tobiasdruckt/SGNode/.openhands/librarian/files/SGNode_Plug_SGNode_Plug.md

# SGNode_Plug/SGNode_Plug.ino

**Type:** Arduino Sketch
**Hash:** `328629a377f053a2d4831d89c57e913e6fd26ec8657b2f4a0ddb5f2aaffe9b44`

## Role

Plug temperature controller entry point with PI control and ESP-NOW communication.

## Verified API / Symbols

## Key Dependencies

- plug_hardware.h, src/air_controller.h, src/beer_pi_controller.h, src/plug_sensors.h, src/plug_selfcheck.h

## Side Effects

- Temperature target calculation

## Tests

- No dedicated automated test identified

## Change Risks

- **MEDIUM**: Core functionality change

---
*Last modified (hash): 328629a377f053a2d4831d89c57e913e6fd26ec8657b2f4a0ddb5f2aaffe9b44*
