tobiasdruckt/SGNode/.openhands/librarian/files/SGNode_Plug_src_air_controller.md

# SGNode_Plug/src/air_controller.h

**Type:** C++ Header
**Hash:** `8307e315ba311d8ae50e1e14f3aa872aa893262df997e26e768ca7ebc397dfbf`

## Role

Fridge air temperature target calculation from beer target.

## Verified API / Symbols

- Structs: AirControllerConfig
- Classes: AirController

- Functions: update, setConfig, relayOn, lastChangeMs

## Key Dependencies

- beer_pi_controller.h

## Side Effects

- No significant side effects

## Tests

- No dedicated automated test identified

## Change Risks

- **MEDIUM**: Core functionality change

---
*Last modified (hash): 8307e315ba311d8ae50e1e14f3aa872aa893262df997e26e768ca7ebc397dfbf*
