tobiasdruckt/SGNode/.openhands/librarian/files/SGNode_Plug_src_plug_types.md

# SGNode_Plug/src/plug_types.h

**Type:** C++ Header
**Hash:** `ce8625bc8ce176ee42a78beea442ccf4ed55586093ea766cdf19b6ec3cb79450`

## Role

Header file with declarations.

## Verified API / Symbols

- Structs: SensorSnapshot
- Classes: PlugControlMode
- Enums: class, PlugFault

## Key Dependencies

- Arduino.h, sg_protocol.h

## Side Effects

- No significant side effects

## Tests

- No dedicated automated test identified

## Change Risks

- **MEDIUM**: Core functionality change

---
*Last modified (hash): ce8625bc8ce176ee42a78beea442ccf4ed55586093ea766cdf19b6ec3cb79450*
