tobiasdruckt/SGNode/.openhands/librarian/files/SGNode_Plug_src_plug_selfcheck_h.md

# SGNode_Plug/src/plug_selfcheck.h

**Type:** C++ Header
**Hash:** `57b49919bb82ef1c21641c5f9edea90fe9c7763b2bc4e47531cef4ad020f714f`

## Overview / Role

Core functionality module

## Verified API & Symbols

No API symbols found or file type not supported

## Key Dependencies

**System/External:**
- `<Arduino.h>`

## Side Effects & Hardware Access

- No significant side effects

## Change Risks

- **MEDIUM**: Core functionality change

---
*Last modified (hash): 57b49919bb82ef1c21641c5f9edea90fe9c7763b2bc4e47531cef4ad020f714f*
