tobiasdruckt/SGNode/.openhands/librarian/files/SGNode_Base_src_calculations_brix_converter.md

# SGNode_Base/src/calculations/brix_converter.h

**Type:** C++ Header
**Hash:** `5e41e067330df2d826816df89a01c500e7435dedcccd328aad6d9078b4e3edc9`

## Role

Brix to SG conversion using calibration polynomial.

## Verified API / Symbols

- Classes: BrixConverter

- Functions: brixToSG

## Key Dependencies

- polynomial_calibration.h

## Side Effects

- No significant side effects

## Tests

- No dedicated automated test identified

## Change Risks

- **MEDIUM**: Calculation changes affect data accuracy

---
*Last modified (hash): 5e41e067330df2d826816df89a01c500e7435dedcccd328aad6d9078b4e3edc9*
