tobiasdruckt/SGNode/.openhands/librarian/files/SGNode_Base_src_calculations_target_curve.md

# SGNode_Base/src/calculations/target_curve.h

**Type:** C++ Header
**Hash:** `1c5d0c6030944191cfbcedbfc1d03d2b40349b1e07c24ff98de612adee10b815`

## Role

Temperature target curve generation.

## Verified API / Symbols

- Classes: TargetCurveGenerator

- Functions: generateAndSave, expectedGravityAtHour, expectedAttenuationAtHour

## Key Dependencies

- brew_profile.h

## Side Effects

- No significant side effects

## Tests

- No dedicated automated test identified

## Change Risks

- **MEDIUM**: Calculation changes affect data accuracy

---
*Last modified (hash): 1c5d0c6030944191cfbcedbfc1d03d2b40349b1e07c24ff98de612adee10b815*
