tobiasdruckt/SGNode/.openhands/librarian/files/SGNode_Base_src_domain_batch_action.md

# SGNode_Base/src/domain/batch_action.h

**Type:** C++ Header
**Hash:** `cc4561e8239351c93ec19e92246e3ac046810b8edf2029d3946a3bc6921fdaf9`

## Role

Batch data structures and state management.

## Verified API / Symbols

- Structs: BatchAction
- Classes: BatchActionEngine
- Enums: BatchActionType

- Functions: applyStyleDefaults, applyDone, applySkip

## Key Dependencies

- Arduino.h
- FS.h, SD.h (for batch persistence)

## Side Effects

- No significant side effects

## Tests

- No dedicated automated test identified

## Change Risks

- **MEDIUM**: Domain logic affects business rules

---
*Last modified (hash): cc4561e8239351c93ec19e92246e3ac046810b8edf2029d3946a3bc6921fdaf9*
