tobiasdruckt/SGNode/.openhands/librarian/files/SGNode_Base_src_domain_fermentation_state_machine.md

# SGNode_Base/src/domain/fermentation_state_machine.h

**Type:** C++ Header
**Hash:** `c94df5f87726f569a1de4751b6daa8bea19875daa21fbb661194700243f60946`

## Role

Fermentation state machine and phase tracking.

## Verified API / Symbols

- Classes: FermentationStateMachine
- Enums: FermentationPhase

- Functions: reset

## Key Dependencies

- Arduino.h
- batch_action.h

## Side Effects

- No significant side effects

## Tests

- No dedicated automated test identified

## Change Risks

- **HIGH**: State machine affects batch tracking

---
*Last modified (hash): c94df5f87726f569a1de4751b6daa8bea19875daa21fbb661194700243f60946*
