tobiasdruckt/SGNode/.openhands/librarian/files/SGNode_Base_src_domain_yeast_preset.md

# SGNode_Base/src/domain/yeast_preset.h

**Type:** C++ Header
**Hash:** `b73fa077c95b8817bcb092ea003f989cab3516cdc6004e01fa5ec9d90076fd9a`

## Role

Yeast preset configuration and repository.

## Verified API / Symbols

- Structs: YeastPreset

## Key Dependencies

- Arduino.h
- FS.h, SD.h (for yeast file storage)

## Side Effects

- No significant side effects

## Tests

- No dedicated automated test identified

## Change Risks

- **MEDIUM**: Domain logic affects business rules

---
*Last modified (hash): b73fa077c95b8817bcb092ea003f989cab3516cdc6004e01fa5ec9d90076fd9a*
