tobiasdruckt/SGNode/.openhands/librarian/files/SGNode_Base_src_domain_yeast_preset_repository.md

# SGNode_Base/src/domain/yeast_preset_repository.h

**Type:** C++ Header
**Hash:** `1a147f964cd8618a893252e45a2800361be83310e576e99de19c2c4fcf8ad808`

## Role

Yeast preset configuration and repository.

## Verified API / Symbols

- Classes: YeastPresetRepository

- Functions: invalidateCache, reloadCustom, count, applyToProfile, isCustom, saveCustom, deleteCustom

## Key Dependencies

- Arduino.h
- FS.h, SD.h (for yeast file storage)

## Side Effects

- No significant side effects

## Tests

- No dedicated automated test identified

## Change Risks

- **MEDIUM**: Domain logic affects business rules

---
*Last modified (hash): 1a147f964cd8618a893252e45a2800361be83310e576e99de19c2c4fcf8ad808*
