tobiasdruckt/SGNode/.openhands/librarian/files/SGNode_Base_src_ui_brew_wizard_controller.md

# SGNode_Base/src/ui/brew_wizard_controller.h

**Type:** C++ Header
**Hash:** `402d01940dfb781f971f2dc086219334e5958b499bc3ebb8d340eff37e6c521d`

## Role

Touchscreen UI components for base station.

## Verified API / Symbols

- Classes: WizardStepper, VirtualKeyboardInput, StyleDropdown, AttenuationDropdown, IOSSwitch
- Enums: BrewWizardStep

- Functions: draw, handleTextTouch, handleNumberTouch, drawText, drawNumber, count, valueAt, hit, begin, handleTouch

## Key Dependencies

- Arduino.h
- TFT_eSPI.h

## Side Effects

- Touchscreen UI updates

## Tests

- No dedicated automated test identified

## Change Risks

- **MEDIUM**: UI changes affect user experience

---
*Last modified (hash): 402d01940dfb781f971f2dc086219334e5958b499bc3ebb8d340eff37e6c521d*
