tobiasdruckt/SGNode/.openhands/librarian/files/SGNode_Base_src_ui_ui_tokens.md

# SGNode_Base/src/ui/ui_tokens.h

**Type:** C++ Header
**Hash:** `b66e78fc84c8e0ac1aaf987366e8da169580bf831fdd6b88a70602f1c9a8864e`

## Role

Touchscreen UI components for base station.

## Verified API / Symbols

- Functions: rgb565, uiInitColors

## Key Dependencies

- Arduino.h
- TFT_eSPI.h

## Side Effects

- No significant side effects

## Tests

- No dedicated automated test identified

## Change Risks

- **MEDIUM**: UI changes affect user experience

---
*Last modified (hash): b66e78fc84c8e0ac1aaf987366e8da169580bf831fdd6b88a70602f1c9a8864e*
