tobiasdruckt/SGNode/.openhands/librarian/files/SGNode_Plug_src_plug_selfcheck.md

# SGNode_Plug/src/plug_selfcheck.h

**Type:** C++ Header
**Hash:** `57b49919bb82ef1c21641c5f9edea90fe9c7763b2bc4e47531cef4ad020f714f`

## Role

Header file with declarations.

## Verified API / Symbols

- Functions: runPlugSelfChecks

## Key Dependencies

- Arduino.h

## Side Effects

- No significant side effects

## Tests

- No dedicated automated test identified

## Change Risks

- **MEDIUM**: Core functionality change

---
*Last modified (hash): 57b49919bb82ef1c21641c5f9edea90fe9c7763b2bc4e47531cef4ad020f714f*
