tobiasdruckt/SGNode/.openhands/librarian/files/SGNode_Plug_src_plug_transport.md

# SGNode_Plug/src/plug_transport.h

**Type:** C++ Header
**Hash:** `c5f03b4bd983e4b1c55153e3edbc8ea55bb9e342c8efd9fb4064104756ac84df`

## Role

ESP-NOW transport layer for Plug communication.

## Verified API / Symbols

- Classes: PlugTransport

- Functions: begin, hasCommand, lastCommandMs, sendStatus, onReceive

## Key Dependencies

- Arduino.h
- sg_protocol.h
- esp_now.h

## Side Effects

- No significant side effects

## Tests

- No dedicated automated test identified

## Change Risks

- **MEDIUM**: Core functionality change

---
*Last modified (hash): c5f03b4bd983e4b1c55153e3edbc8ea55bb9e342c8efd9fb4064104756ac84df*
