tobiasdruckt/SGNode/RELEASE_NOTES_v0.3.0-alpha.md

# SGNode v0.3.0-alpha Release Notes

> Historical archive. Current documentation and active release notes are in `README.md` and `RELEASE_NOTES_v0.5.0-alpha.md`.

**Release Date:** May 6, 2026  
**Status:** Design Freeze - Alpha Release  

## Overview

SGNode v0.3.0-alpha marks a significant milestone with complete system stabilization, comprehensive calibration functionality, and robust data management. This release introduces critical fixes for polynomial calibration, SD card file corruption, and battery voltage accuracy, establishing a solid foundation for fermentation monitoring.

## 🎯 Design Freeze Features

### Confirmed Working Systems
- ✅ **Peer-to-Peer Communication** - Reliable ESP-NOW data transmission with retry logic
- ✅ **Calibration System** - Complete 4-point calibration with 3rd degree polynomial calculation
- ✅ **Data Logging** - Robust CSV file creation and SD card storage with corruption prevention
- ✅ **Real-time Display** - Live, Graph, and Detail views with immediate data display after reboot
- ✅ **Battery Monitoring** - Accurate voltage measurement with calibrated voltage divider
- ✅ **Historical Data Persistence** - Automatic data loading and file continuation across reboots

### System Safeguards
- 🛡️ **Communication Reliability** - CRC16 verification, peer management, channel forcing
- 🛡️ **Sensor Protection** - Initialization retry, watchdog timer, voltage sanity checks
- 🛡️ **Calibration Safety** - Matrix singularity detection, coefficient validation, EEPROM versioning
- 🛡️ **File System Protection** - Write verification, extension validation, automatic recovery
- 🛡️ **Power Management** - GPIO optimization, deep sleep protection, battery monitoring

## 🔧 Critical Fixes

### Polynomial Calibration System
- **Fixed matrix back substitution** - Corrected RHS extraction from augmented matrix
- **Fixed coefficient mapping** - Simplified nested ternary operators to clear if/else structure
- **Added debug output** - Coefficient logging for verification and troubleshooting
- **Result**: Calibration now produces accurate polynomial coefficients instead of all zeros

### Base Station Communication
- **Fixed rate limiting** - Reset rate limiting before final calibration response transmission
- **Enhanced error handling** - Better ESP-NOW error reporting and recovery
- **Result**: Base station receives completion message and shows "Calibration Success"

### SD Card File System
- **Fixed file corruption** - Added filename validation preventing .c file creation
- **Enhanced file management** - Sequential numbering (fermentation_001.csv, etc.)
- **Added historical loading** - Automatic CSV data loading on reboot (up to 100 points)
- **Result**: No more corrupted files, seamless data continuation across reboots

### Battery Voltage Accuracy
- **Updated calibration factor** - Changed from 0.913 to 1.048 (13% error correction)
- **Added voltage divider spec** - 51kΩ:51kΩ with 10µF filtering capacitor
- **Enhanced SOC calculation** - More accurate battery percentage display
- **Result**: 4.062V battery now reads correctly as ~4.06V

## 📊 Technical Improvements

### Data Management
- **CSV format standardization** - Consistent column ordering and metadata
- **OG capture persistence** - Original Gravity restored from CSV comments on reboot
- **File integrity verification** - Byte count validation for all SD writes
- **Automatic file recovery** - Creates new file if corruption detected

### Power Optimization
- **Deep sleep enhancement** - Proper WiFi/ESP-NOW deinitialization
- **GPIO leakage prevention** - All unused pins configured as OUTPUT LOW
- **Battery monitoring** - Real-time SOC with low-battery warnings
- **Charging protection** - Built-in over-charge/discharge protection

### User Experience
- **Calibration wizard reliability** - Consistent command transmission and response
- **Immediate data display** - Views show historical data immediately after reboot
- **Touch interface responsiveness** - Improved navigation and status indicators
- **Debug system** - Comprehensive conditional compilation levels

## 🔧 Hardware Specifications

### Float Unit
- **WeMos D32 ESP32** with built-in 18650 battery holder
- **BMI160 IMU** - 6-axis accelerometer/gyroscope
- **BMP180** - Temperature/pressure sensor
- **Voltage Divider** - 51kΩ:51kΩ with 10µF capacitor
- **Calibration Switch** - GPIO12 hardware switch activation

### Base Station
- **4.0inch ESP32-32E** - Integrated display with touch screen
- **SD Card Support** - FAT32 formatted, 4GB+ recommended
- **Power Supply** - 5V USB, ~290mA consumption

## 📈 Performance Metrics

### Accuracy
- **Tilt measurement**: ≤0.5° angle resolution
- **SG accuracy**: ±0.001 with proper calibration
- **Temperature**: ±0.1°C with EMA filtering
- **Battery voltage**: ±1% after calibration

### Battery Life
- **Float continuous**: 17+ hours
- **Float deep sleep**: 2-4 weeks (2000mAh 18650)
- **Base station**: Continuous operation on USB power

### Communication
- **Range**: ~50m line of sight
- **Update rate**: 60-600 seconds (default 180s)
- **Reliability**: CRC16 verification, 3-retry logic

## 🚀 Future Roadmap (Post-Alpha)

### Planned Improvements
- **UI and Theme Enhancements** - Improved visual design and user interface
- **Clock Integration** - Real-time clock in base station
- **3D Printed Housing** - Waterproof float enclosure design
- **Liquid Behavior Testing** - Real-world fermentation testing
- **Enhanced Data Visualization** - Improved graphs and analytics
- **Wireless Configuration** - OTA updates and remote configuration

### Development Focus
- **User Experience** - Streamlined setup and operation
- **Data Analysis** - Advanced fermentation analytics
- **Connectivity** - Enhanced wireless features
- **Power Efficiency** - Further battery optimization

## 📋 Installation Requirements

This library and hardware list describes the archived v0.3.0 build only. Current requirements are documented in `README.md`.

### Required Libraries
- **Float Unit**: EmotiBit BMI160, Adafruit BMP085
- **Base Station**: TFT_eSPI, SD (built-in), FS (built-in)

### Hardware Components
- **Float Unit**: WeMos D32, BMI160, BMP180, 18650 battery, SPST switch
- **Base Station**: 4.0inch ESP32-32E display, MicroSD card, USB power

### Setup Steps
1. Install required libraries via Arduino IDE
2. Configure base station MAC address in float unit
3. Upload firmware to both devices
4. Perform 4-point calibration
5. Start fermentation monitoring

## 🎯 Design Freeze Status

This v0.3.0-alpha release establishes a **design freeze** for the core functionality. All confirmed features are working reliably, and the system is ready for real-world testing.

### What's Frozen
- ✅ Core communication protocol (ESP-NOW)
- ✅ Calibration system and algorithms
- ✅ Data logging and file management
- ✅ User interface and navigation
- ✅ Battery monitoring and power management
- ✅ Safety systems and error handling

### What's Open for Development
- 🔧 UI themes and visual improvements
- 🔧 Clock integration and time features
- 🔧 3D printed housing design
- 🔧 Advanced analytics and data visualization
- 🔧 Wireless configuration and OTA updates

## 📝 Support and Documentation

- **README.md** - Comprehensive setup and operation guide
- **WIRING_DIAGRAM.md** - Detailed hardware connections
- **hardware.md** - Bill of materials and specifications
- **CHANGELOG.md** - Complete version history
- **Serial Monitor** - Debug output and troubleshooting

---

**This release represents a stable foundation for fermentation monitoring with all core features confirmed working. The system is ready for practical use and further development of advanced features.**
