tobiasdruckt/SGNode/SGNode_Base/SGNode_Base.ino

/*
 * Fermentation Monitor - Base Station
 * Receives data via ESP-NOW and displays on TFT with touch interface
 * Shows real-time data and historical graphs
 * 
 * REQUIRED LIBRARIES (install via Arduino Library Manager):
 * - TFT_eSPI (by Bodmer) - includes built-in touch support
 * - SD (built-in)
 * - FS (built-in)
 * - SPI (built-in)
 */

#include <WiFi.h>
#include <esp_now.h>
#include <WebServer.h>
#include <Update.h>
#include <TFT_eSPI.h>
#include <FS.h>
#include <SD.h>
#include <SPI.h>
#include <Wire.h>
#include <EEPROM.h>
#include <time.h>
#include <sys/time.h>
#include "src/assets/Logo2_Optimized.h"
#include "src/ui/ui_tokens.h"
#include "src/ui/ui_components.h"
#include "src/domain/brew_profile.h"
#include "src/ui/brew_wizard_controller.h"
#include "src/calculations/brix_converter.h"
#include "src/calculations/og_verifier.h"
#include "src/calculations/derived_calculations.h"
#include "src/calculations/target_curve.h"
#include "src/domain/fermentation_state_machine.h"
#include "src/domain/recommendation_engine.h"
#include "src/calculations/eta_predictor.h"
#include "src/domain/batch_action.h"
#include "src/domain/yeast_preset_repository.h"
#include "src/domain/temperature_profile.h"
#ifndef SGNODE_UI_TEST_HARNESS
#define SGNODE_UI_TEST_HARNESS 0  // Debug-only serial UI harness. Keep disabled for production builds.
#endif
#ifndef SGNODE_UI_TEST_MINIMAL
#define SGNODE_UI_TEST_MINIMAL 0  // 1 = minimal harness commands (no UI injection path)
#endif

#ifndef SGNODE_BATTERY_DEBUG
#define SGNODE_BATTERY_DEBUG 0  // Tiny serial diagnostics for battery/history checks. Disabled in production.
#endif
#include "src/test/ui_test_harness.h"
#include "../SGNode_Shared/sg_protocol.h"
#include "../SGNode_Shared/sg_logo_png.h"
#include "src/calculations/polynomial_calibration.h"

#define ACK_PACKET_TYPE 0xA5

// 4.0inch ESP32-32E Display configuration - ST7796S landscape mode
#define SCREEN_W    480  // Landscape width (320x480 native rotated)
#define SCREEN_H    320  // Landscape height
#define DISPLAY_CS  15   // LCD Chip Select
#define DISPLAY_DC  2    // Data/Command
#define DISPLAY_RST -1   // Reset (uses ESP32 reset)

// Custom color definitions (TFT_eSPI doesn't have TFT_GRAY)
#define TFT_GRAY 0x8410  // Dark gray color

enum DebugLevel {
  DEBUG_QUIET = 0,
  DEBUG_ERROR = 1,
  DEBUG_INFO = 2,
  DEBUG_VERBOSE = 3
};

#ifndef SGNODE_DEBUG_LEVEL
#define SGNODE_DEBUG_LEVEL DEBUG_ERROR
#endif

#define LOG_ERROR(...) do { if (SGNODE_DEBUG_LEVEL >= DEBUG_ERROR) Serial.printf(__VA_ARGS__); } while (0)
#define LOG_ERRORLN(msg) do { if (SGNODE_DEBUG_LEVEL >= DEBUG_ERROR) Serial.println(msg); } while (0)
#define LOG_INFO(...) do { if (SGNODE_DEBUG_LEVEL >= DEBUG_INFO) Serial.printf(__VA_ARGS__); } while (0)
#define LOG_INFOLN(msg) do { if (SGNODE_DEBUG_LEVEL >= DEBUG_INFO) Serial.println(msg); } while (0)
#define LOG_VERBOSE(...) do { if (SGNODE_DEBUG_LEVEL >= DEBUG_VERBOSE) Serial.printf(__VA_ARGS__); } while (0)
#define LOG_VERBOSELN(msg) do { if (SGNODE_DEBUG_LEVEL >= DEBUG_VERBOSE) Serial.println(msg); } while (0)

// Theme system for UI
struct Theme {
  // Background colors
  uint16_t background;
  uint16_t cardBackground;
  uint16_t buttonInactive;
  
  // Primary colors
  uint16_t primary;
  uint16_t primaryText;
  
  // Accent colors
  uint16_t accent;
  uint16_t accentText;
  uint16_t gold;  // Gold accent color
  
  // Text colors
  uint16_t textPrimary;
  uint16_t textSecondary;
  uint16_t textMuted;
  
  // Status colors
  uint16_t success;
  uint16_t warning;
  uint16_t error;
  uint16_t info;
  
  // Border colors
  uint16_t border;
  uint16_t gridLine;
  
  // Graph line colors
  uint16_t graphPurple;  // For ABV
  uint16_t graphBlue;    // For SG
  uint16_t graphGreen;   // For Temperature
};

// Light mode theme (default)
Theme lightTheme = {
  .background = rgb565(244, 246, 249),      // Soft cool paper
  .cardBackground = rgb565(238, 241, 246),  // Quiet card surface
  .buttonInactive = rgb565(225, 230, 238),  // Gentle inactive controls
  .primary = rgb565(233, 238, 245),         // Soft top bar
  .primaryText = rgb565(26, 40, 56),        // Soft navy text
  .accent = rgb565(226, 232, 241),          // Subtle accent surface
  .accentText = rgb565(255, 255, 255),     // White
  .gold = rgb565(185, 142, 58),            // Softer amber accent
  .textPrimary = rgb565(26, 34, 46),       // Deep slate (less harsh than black)
  .textSecondary = rgb565(64, 76, 92),     // Secondary slate
  .textMuted = rgb565(108, 120, 136),      // Muted slate
  .success = rgb565(74, 154, 94),          // Softer green
  .warning = rgb565(206, 141, 43),         // Softer amber
  .error = rgb565(203, 89, 89),            // Softer red
  .info = rgb565(73, 132, 196),            // Softer blue
  .border = rgb565(206, 214, 224),         // Soft border
  .gridLine = rgb565(219, 226, 235),       // Soft grid
  .graphPurple = rgb565(142, 100, 174),    // Muted purple for ABV
  .graphBlue = rgb565(73, 132, 196),       // Muted blue for SG
  .graphGreen = rgb565(74, 154, 94)        // Muted green for Temperature
};

// Dark mode theme
Theme darkTheme = {
  .background       = rgb565(11, 31, 42),     // Logo-Farbe
  .cardBackground   = rgb565(22, 30, 56),
  .buttonInactive   = rgb565(38, 48, 74),

  .primary          = rgb565(8, 18, 32),
  .primaryText      = rgb565(255, 255, 255),

  .accent           = rgb565(22, 30, 56),
  .accentText       = rgb565(255, 255, 255),

  .gold             = rgb565(235, 190, 92),

  .textPrimary      = rgb565(255, 255, 255),
  .textSecondary    = rgb565(215, 224, 235),
  .textMuted        = rgb565(160, 174, 192),

  .success          = rgb565(46, 204, 113),
  .warning          = rgb565(255, 193, 7),
  .error            = rgb565(255, 82, 82),
  .info             = rgb565(64, 169, 255),

  .border           = rgb565(45, 55, 80),
  .gridLine         = rgb565(35, 45, 65),

  .graphPurple      = rgb565(180, 100, 255),
  .graphBlue        = rgb565(64, 169, 255),
  .graphGreen       = rgb565(46, 204, 113)
};

// Current theme and mode
Theme* currentTheme = &darkTheme;
bool darkMode = true;

// Screen dirty flag for efficient display updates
bool screenDirty = true;
bool staticElementsDrawn = false;

// Region-based dirty flags for LIVE view
bool heroDirty = true;
bool tileTempDirty = true;
bool tileAngleDirty = true;
bool topbarDirty = true;

// Dirty flags for LIVE_DETAILS_VIEW (Battery display there only)
bool tileAbvDirty = true;  // Now used in LIVE_VIEW for ABV tile
bool detailsDirty = true;

// Touch screen uses TFT_eSPI built-in support (shares SPI with display)
// Touch controller is physically wired to display SPI pins (12,13,14)

// Time-based SPI separation approach
// Create separate SPI instance for SD card to avoid TFT/touch conflicts
SPIClass sdSPI(HSPI);

// SD card pin assignment (using standard ESP32 pins to avoid TFT/touch conflicts)
// TFT and touch use pins 12,13,14, so we use different pins for SD
#define SD_CS       5   // SD card chip select
#define SD_MOSI    23   // SD card SPI bus write data signal
#define SD_MISO    19   // SD card SPI bus read data signal  
#define SD_SCK     18   // SD card SPI bus clock signal

// SD card enable/disable flag
#define SD_ENABLED  true

// DS3230/DS323x RTC on the base station I2C bus
#define RTC_SDA_PIN 32
#define RTC_SCL_PIN 25
#define RTC_I2C_ADDR 0x68
#define RTC_COMPILE_UPLOAD_OFFSET_S 11
#define RTC_VALID_FROM_YEAR 2024

// ESP-NOW configuration
#define ESPNOW_CHANNEL 1

// Data buffering system to avoid real-time SD operations
#define MAX_DATA_BUFFER 500  // Buffer up to 500 sensor readings (increased from 100)
struct BufferedData {
  payload_t data;
  uint32_t epoch_s;
  unsigned long buffered_millis;
  bool written;
};
BufferedData dataBuffer[MAX_DATA_BUFFER];
int bufferIndex = 0;
int bufferedCount = 0;

// SD card management variables
bool sdInitialized = false;
bool sdCardPresent = false;
bool sdWriteErrorActive = false;
unsigned long lastSDWriteFailure = 0;
unsigned long oldestBufferedMillis = 0;
unsigned long lastSDWrite = 0;
const unsigned long SD_WRITE_INTERVAL = 5000;  // Write to SD every 5 seconds
unsigned long lastTouchTime = 0;
const unsigned long TOUCH_TIMEOUT = 3000;     // 3 seconds of inactivity before SD operations

// Data buffer for historical data (display)
#define MAX_DATA_POINTS 150
payload_t displayDataBuffer[MAX_DATA_POINTS];
uint32_t displayTimestampBuffer[MAX_DATA_POINTS];
int displayDataIndex = 0;
int displayDataCount = 0;
float postPackageTempGraphValues[MAX_DATA_POINTS];
uint32_t postPackageTempGraphEpochs[MAX_DATA_POINTS];
int postPackageTempGraphCount = 0;
bool postPackageTempGraphLoadAttempted = false;
char postPackageTempGraphLoadedFile[80] = "";
payload_t latestFloatData = {0};
uint32_t latestFloatEpoch = 0;
bool latestFloatDataValid = false;
uint16_t lastAckedFloatSeq = 0;
uint16_t highestSeenFloatSeq = 0;
uint16_t recentFloatSeqs[16] = {0};
uint8_t recentFloatSeqIndex = 0;
uint8_t recentFloatSeqCount = 0;
uint32_t duplicateFloatPackets = 0;
int totalCSVDataLines = 0;  // Total data points in CSV file
int lastHistoricalLoadedLines = 0;
int lastHistoricalSkippedLines = 0;
int lastHistoricalParseErrors = 0;
int lastHistoricalPreBatchLines = 0;
int lastHistoricalPostBatchLines = 0;
int lastHistoricalBatchFilteredLines = 0;
int lastHistoricalCutoffFilteredLines = 0;
bool lastHistoricalBatchStartRelaxed = false;
uint32_t lastHistoricalOldestEpoch = 0;
uint32_t lastHistoricalNewestEpoch = 0;
uint32_t lastPostPackageTempLogMs = 0;
uint32_t lastPostPackageFloatPacketMs = 0;
payload_t lastPostPackageFloatPacket = {0};
uint32_t lastPostPackageFloatPacketEpoch = 0;
bool lastPostPackageFloatPacketValid = false;

#define CSV_LINE_BUFFER_SIZE 384
#define FERMENTATION_LOG_HEADER "timestamp,epoch_s,uptime_s,angle,density,temperature,battery_voltage,battery_percent,state,current_attenuation,estimated_abv,recommendation_code,float_temperature,plug_beer_temperature,plug_air_temperature,plug_beer_target,plug_air_target,plug_mode,plug_relay,plug_duty_10m,plug_faults,plug_pi_offset,plug_pi_tn,plug_beer_rate,plug_kp,plug_d_brake,plug_p_offset,plug_i_offset,plug_d_offset,plug_ramp_trim,plug_ramp_i,plug_ramp_rate_error,plug_beer_rate_raw"
#define POST_PACKAGE_TEMP_LOG_INTERVAL_MS (10UL * 60UL * 1000UL)

// Separate buffer for discharge rate calculation (25 recent points only)
payload_t dischargeRateBuffer[25];
uint32_t dischargeRateTimestampBuffer[25];
int dischargeRateBufferCount = 0;

// Cursor state for graph view
int cursorIndex = 0;           // Index of selected data point
float cursorPosition = 1.0;    // 0.0 to 1.0 (0% to 100% of X-axis)

// Graph data loading mode
enum GraphLoadMode { LOAD_6H, LOAD_24H, LOAD_ALL };
GraphLoadMode currentLoadMode = LOAD_6H;
GraphLoadMode batteryLoadMode = LOAD_6H;

// RSSI tracking for ESP-NOW signal strength
int lastRSSI = 0;
bool rssiAvailable = false;

// Graph points for polynomial display
struct GraphPoint {
  int x;
  int y;
  bool valid;
};
GraphPoint graphPoints[91];

// ABV calculation variables
float originalGravity = 0.0;  // OG captured when stable
float currentABV = 0.0;       // Calculated ABV
int readingCount = 0;         // Number of readings since fermentation started
float last3Readings[3] = {0.0, 0.0, 0.0}; // Last 3 SG readings for stability check
bool ogCaptured = false;      // Whether OG has been captured
#define OG_STABILITY_THRESHOLD 0.005 // SG variance threshold for stability
#define OG_MAX_READINGS 10     // Force capture at this reading if not stable

// Battery tracking variables
enum ChargingState {
  CHARGING_UNKNOWN,
  CHARGING,
  DISCHARGING
};
ChargingState chargingState = CHARGING_UNKNOWN;
float lastBatteryVoltage = 0.0;
unsigned long lastBatteryCheck = 0;

// Display objects - TFT_eSPI includes built-in XPT2046 touch support
TFT_eSPI tft = TFT_eSPI();

// UI state
enum ViewMode {
  LIVE_VIEW,
  GRAPH_VIEW,
  CALIBRATION_VIEW,
  BATTERY_VIEW,
  MORE_VIEW,
  LIVE_DETAILS_VIEW,
  POLY_GRAPH_VIEW,
  TEMP_GRAPH_VIEW,
  ANGLE_GRAPH_VIEW,
  ABV_GRAPH_VIEW
  ,
  BREW_WIZARD_VIEW,
  OG_VERIFICATION_VIEW,
  TARGET_CHART_VIEW,
  DASHBOARD_VIEW,
  NEW_YEAST_VIEW,
  MANAGE_YEAST_VIEW,
  MANAGE_BREW_VIEW,
  PLUG_GOVERNOR_VIEW
};

ViewMode currentMode = LIVE_VIEW;

// Graph metric types for parameterized graph drawing
enum GraphMetric { METRIC_DENSITY, METRIC_TEMPERATURE, METRIC_ANGLE, METRIC_ABV };
enum TempGraphMode { TEMP_GRAPH_FERMENT, TEMP_GRAPH_POST_PACKAGE };
TempGraphMode tempGraphMode = TEMP_GRAPH_FERMENT;

// Calibration state
enum CalibMode {
  CALIB_IDLE,
  CALIB_SETUP,
  CALIB_INSTRUCTIONS,
  CALIB_OFFSET,
  CALIB_POINT1,
  CALIB_POINT2,
  CALIB_POINT3,
  CALIB_POINT4,
  CALIB_POINT5,
  CALIB_POINT6,
  CALIB_COMPLETE,
  CALIB_APPLYING,
  CALIB_FAILED,
  CALIB_SKIP_WARNING
};

CalibMode calibMode = CALIB_IDLE;
static const int MAX_BASE_CALIB_POINTS = 6;
float calibAngles[MAX_BASE_CALIB_POINTS] = {0.0, 0.0, 0.0, 0.0, 0.0, 0.0};
float calibSG[MAX_BASE_CALIB_POINTS] = {1.000, 1.010, 1.020, 1.030, 1.045, 1.060};
int sugarAmounts4[4] = {0, 107, 115, 124}; // Approx. incremental grams for 2kg water
int sugarAmounts6[6] = {0, 53, 54, 56, 89, 94};
int saltAmounts4[4] = {0, 58, 63, 60}; // Approx. incremental grams for 2kg water at 20C
int saltAmounts6[6] = {0, 29, 29, 29, 49, 45};
bool calibDoSGCalibration = true;
bool calibUseSixPoints = false;
bool calibUseSalt = false;
float calibOffset = 0.0; // Store sensor offset angle
bool offsetCalibrated = false; // Track if offset calibration is complete
uint8_t currentRequestId = 0;
bool calibrationModeActive = false; // Track if float is in calibration mode
char calibFailureMessage[64] = "No response from float";

// Wait notification system
unsigned long waitStartTime = 0;
bool waitActive = false;
int waitDuration = 0; // Duration in milliseconds
float calibWaitEtaSeconds = -1.0f;
float calibWaitTempDriftPerMin = 0.0f;
uint32_t calibWaitStatusMs = 0;
char calibWaitStatus[32] = "Measuring...";

// Calibration response flood protection
unsigned long lastCalibrationResponse = 0;
const unsigned long CALIBRATION_RESPONSE_RATE_LIMIT = 500; // 500ms minimum between responses (reduced from 1000ms)
int calibrationResponseCount = 0;
const int MAX_CALIBRATION_RESPONSES_PER_MINUTE = 30; // Max 30 responses per minute


// Float unit MAC address storage
uint8_t floatMac[6] = {0}; // Store float unit MAC address
bool floatMacKnown = false; // Flag to indicate if float MAC is known
uint8_t plugMac[6] = {0};
bool plugMacKnown = false;
sg_plug_status_t latestPlugStatus = {};
bool latestPlugStatusValid = false;
uint32_t latestPlugStatusMs = 0;
float latestPlugPComponentC = NAN;
float latestPlugIComponentC = NAN;
float latestPlugDComponentC = NAN;
float latestPlugRampTrimC = NAN;
float latestPlugRampITrimC = NAN;
float latestPlugRampRateErrorKPerHour = NAN;
float latestPlugBeerRateRawCPerHour = NAN;
bool latestPlugComponentsValid = false;
uint16_t plugCommandSequence = 0;
uint32_t lastPlugCommandMs = 0;
float latestFloatTemperatureC = NAN;
float lastValidPlugBeerTemperatureC = NAN;
uint8_t plugBeerTemperatureMissCount = 0;
constexpr float PLUG_DEFAULT_CONTROLLER_KP = 0.45f;
constexpr float PLUG_DEFAULT_CONTROLLER_TN_H = 0.75f;
constexpr float PLUG_DEFAULT_CONTROLLER_D_BRAKE_H = 0.8f;
float plugControllerKp = PLUG_DEFAULT_CONTROLLER_KP;
float plugControllerTnHours = PLUG_DEFAULT_CONTROLLER_TN_H;
float plugControllerDBrakeHours = PLUG_DEFAULT_CONTROLLER_D_BRAKE_H;

struct PlugGovernorSettings {
  float kp;
  float integralTnHours;
  float dBrakeHours;
  float airTurnOffAboveTargetC;
  float airTurnOnAboveTargetC;
  uint16_t airMinimumOnS;
  uint16_t airMinimumOffS;
  float coldIntegralBandC;
  float warmIntegralBandC;
  float maxPositiveIntegralC;
  float maxNegativeIntegralC;
  float integralLeakPerHour;
  float errorCrossingKeepFactor;
  float maxDOffsetC;
  float warmingDFactor;
  float beerUndershootLockoutC;
  float fastWarmingRateKPerH;
  float strongUndershootC;
  float strongUndershootAirOffsetC;
  float minAirTargetC;
  float maxAirTargetC;
  float targetStepC;
  float rampControllerKpHours;
  float rampControllerTnHours;
  float maxRampTrimC;
  float rampFadeDistanceC;
  float rateFilterSamples;
};

PlugGovernorSettings plugGovSettings = {};
bool plugGovSettingsLoaded = false;
bool plugGovSettingsDirty = false;
bool plugGovLastSaveOk = true;
uint8_t plugGovSelectedIndex = 0;
uint8_t plugGovFirstVisibleIndex = 0;
uint8_t plugDetailsTapCount = 0;
uint32_t plugDetailsTapWindowStartMs = 0;
const char PLUG_GOV_SETTINGS_DIR[] = "/data/plug";
const char PLUG_GOV_SETTINGS_PATH[] = "/data/plug/gov_settings.json";
constexpr uint8_t PLUG_GOV_SETTING_COUNT = 27;

struct PlugTestPhase {
  float targetC;
  uint32_t holdSeconds;
  float minBeerC;
  bool hasMinBeerC;
};
PlugTestPhase plugTestPhases[5];
uint8_t plugTestPhaseCount = 0;
uint8_t plugTestPhaseIndex = 0;
bool plugTestScheduleLoaded = false;
bool plugTestScheduleEnabled = false;
bool plugTestStarted = false;
bool plugTestPhaseReached = false;
float plugTestReachToleranceC = 0.3f;
uint32_t plugTestStartedEpoch = 0;
uint32_t plugTestPhaseReachedEpoch = 0;
char plugTestLoadedBatchId[24] = "";

// EEPROM addresses for float MAC storage
#define EEPROM_BYTES 160
#define EEPROM_FLOAT_MAC_MAGIC 100
#define EEPROM_FLOAT_MAC_ADDR 104
#define EEPROM_THEME_MAGIC 120
#define EEPROM_THEME_VALUE 124
#define EEPROM_PLUG_MAC_MAGIC 132
#define EEPROM_PLUG_MAC_ADDR 136
#define EEPROM_BRIGHTNESS_MAGIC 148
#define EEPROM_BRIGHTNESS_VALUE 152
#define FLOAT_MAC_MAGIC 0x4D414346 // "MACF" in hex
#define THEME_MAGIC 0x54484D45 // "THME" in hex
#define PLUG_MAC_MAGIC 0x4D414350 // "MACP" in hex
#define BRIGHTNESS_MAGIC 0x54494C42 // "BLIT" in hex

#define TFT_BACKLIGHT_PIN 27
#define BACKLIGHT_PWM_CHANNEL 7
#define BACKLIGHT_PWM_FREQ 5000
#define BACKLIGHT_PWM_RESOLUTION 8

// Touch handling
uint16_t touchX, touchY;
#if SGNODE_UI_TEST_HARNESS
struct UITestObject {
  const char* id;
  const char* type;
  const char* label;
  int x;
  int y;
  int w;
  int h;
  bool enabled;
  bool visible;
};

bool uiTestTouchActive = false;
uint16_t uiTestTouchX = 0;
uint16_t uiTestTouchY = 0;
unsigned long uiTestMockTime = 0;
payload_t uiTestMockPayload = {0};
bool uiTestMockSGSet = false;
bool uiTestMockTempSet = false;
#endif

// Timing
unsigned long lastUpdate = 0;
unsigned long lastTouchCheck = 0;
const unsigned long TOUCH_CHECK_INTERVAL = 50; // ms
unsigned long lastTopbarRefresh = 0;
const unsigned long TOPBAR_REFRESH_INTERVAL = 10000; // ms

// Button areas for touch interface
#define BUTTON_LIVE_X 10
#define BUTTON_LIVE_Y 10
#define BUTTON_LIVE_W 60
#define BUTTON_LIVE_H 30

#define BUTTON_GRAPH_X 80
#define BUTTON_GRAPH_Y 10
#define BUTTON_GRAPH_W 60
#define BUTTON_GRAPH_H 30

#define BUTTON_CALIB_X 150
#define BUTTON_CALIB_Y 10
#define BUTTON_CALIB_W 80
#define BUTTON_CALIB_H 30

// Reboot prompt buttons
#define BUTTON_CONTINUE_X 60
#define BUTTON_CONTINUE_Y 140
#define BUTTON_CONTINUE_W 100
#define BUTTON_CONTINUE_H 40

#define MANAGE_BREW_ROW_Y 184
#define MANAGE_BREW_ROW_H 34
#define MANAGE_BREW_NAV_W 48
#define MANAGE_BREW_ACTION_W 90
#define MANAGE_BREW_PREV_X MARGIN
#define MANAGE_BREW_CONT_X (MARGIN + 60)
#define MANAGE_BREW_COPY_X (MARGIN + 162)
#define MANAGE_BREW_DELETE_X (MARGIN + 264)
#define MANAGE_BREW_NEXT_X (UI_W - MARGIN - MANAGE_BREW_NAV_W)

#define BUTTON_NEW_X 160
#define BUTTON_NEW_Y 140
#define BUTTON_NEW_W 100
#define BUTTON_NEW_H 40

// Create New Fermentation dialog buttons
#define BUTTON_DIALOG_YES_X 80
#define BUTTON_DIALOG_YES_Y 180
#define BUTTON_DIALOG_YES_W 100
#define BUTTON_DIALOG_YES_H 40

#define BUTTON_DIALOG_BACK_X 220
#define BUTTON_DIALOG_BACK_Y 180
#define BUTTON_DIALOG_BACK_W 100
#define BUTTON_DIALOG_BACK_H 40

// SD card and file management
char currentFermentationFile[64] = "";
bool fermentationFileOpen = false;
bool showingCreateNewDialog = false;

// Phase 1 intelligent fermentation assistant state
BrewProfile activeBrewProfile;
BrewWizardController brewWizard;
OGVerifier ogVerifier;
FermentationStateMachine fermentationStateMachine;
DerivedMetrics fermentationMetrics = {1.000f, 0.0f, 0.0f, 0.0f, 0.0f};
Recommendation currentRecommendation = {0, "Start Brew Wizard to enable guidance"};
BatchAction currentBatchAction = {ACTION_NONE, 0, false, 0, "Next", "No action required"};
ETAResult currentETA = {0, 0, false, false, 0};
bool brewProfileLoaded = false;
bool brewWizardHasSavedRuntime = false;
BrewProfile brewWizardSavedProfile;
bool brewWizardSavedProfileLoaded = false;
bool brewWizardSavedFermentationFileOpen = false;
char brewWizardSavedFermentationFile[sizeof(currentFermentationFile)] = "";
bool ogVerificationPending = false;
bool targetCurveAvailable = false;
bool yeastPerformanceSaved = false;
float previousAnalyticsSG = 0.0f;
uint32_t previousAnalyticsEpoch = 0;
bool floatZeroCalCommandPending = false;
bool floatZeroCalAwaitingConfirmation = false;
uint8_t floatZeroCalCommandId = 0;
char floatZeroCalStatus[80] = "";

WebServer baseOtaServer(80);
bool baseOtaActive = false;
bool baseOtaUploadInProgress = false;
unsigned long baseOtaStartedMs = 0;
unsigned long baseOtaLastClientMs = 0;
char baseOtaSsid[32] = "";
bool baseOtaConfirmVisible = false;
bool baseOtaStaticDrawn = false;

bool floatOtaPopupVisible = false;
char floatOtaPopupSsid[32] = "";
char floatOtaPopupIp[18] = "";
uint16_t floatOtaPopupTimeoutS = 0;

bool topbarPulldownVisible = false;
bool topbarDragCandidate = false;
uint16_t topbarDragStartY = 0;
unsigned long topbarDragStartMs = 0;

uint8_t backlightLevel = 2;
const uint8_t BACKLIGHT_DUTY_LEVELS[] = {10, 50, 120, 255};

enum NewYeastStep {
  NY_NAME,
  NY_CATEGORY,
  NY_ATT_MIN,
  NY_ATT_MAX,
  NY_ATT_DEFAULT,
  NY_SPEED,
  NY_LAG,
  NY_DURATION,
  NY_TEMP_MIN,
  NY_TEMP_MAX,
  NY_FLOC,
  NY_CURVE,
  NY_DREST,
  NY_NOTES,
  NY_REVIEW
};

struct EditableYeastPreset {
  char id[24];
  char displayName[32];
  char category[32];
  int typicalAttenuationMin;
  int typicalAttenuationMax;
  int defaultAttenuation;
  char fermentationSpeed[16];
  float lagPhaseHours;
  float typicalDurationHours;
  float recommendedTempMinC;
  float recommendedTempMaxC;
  char flocculation[16];
  char curveTemplate[32];
  bool diacetylRestRecommended;
  char notes[64];
};

EditableYeastPreset yeastDraft;
NewYeastStep newYeastStep = NY_NAME;
char yeastEditBuffer[64] = "";
bool yeastEditPristine = false;
bool editingExistingYeast = false;
int manageYeastIndex = 0;
char managedYeastIds[12][24];
char managedYeastNames[12][32];
int managedYeastCount = 0;
int manageBatchIndex = 0;
char managedBatchIds[16][24];
char managedBatchNames[16][40];
int managedBatchCount = 0;
bool manageBrewCompleteConfirm = false;

struct ManagedBatchSummary {
  bool loaded;
  bool completed;
  bool postPackageTracking;
  char style[24];
  float liters;
  int points;
  uint32_t firstEpoch;
  uint32_t lastEpoch;
  char status[18];
  char evaluation[32];
};

// Calibration buttons (step-by-step wizard) - reorganized for consistent layout
#define BUTTON_CALIB_START_X (UI_W - MARGIN - 132)
#define BUTTON_CALIB_START_Y 236
#define BUTTON_CALIB_START_W 132
#define BUTTON_CALIB_START_H 36

#define BUTTON_CALIB_BACK_X MARGIN
#define BUTTON_CALIB_BACK_Y 236
#define BUTTON_CALIB_BACK_W 132
#define BUTTON_CALIB_BACK_H 36

#define BUTTON_CALIB_NEXT_X (UI_W - MARGIN - 132)
#define BUTTON_CALIB_NEXT_Y 236
#define BUTTON_CALIB_NEXT_W 132
#define BUTTON_CALIB_NEXT_H 36

#define BUTTON_CALIB_APPLY_X (UI_W - MARGIN - 132)
#define BUTTON_CALIB_APPLY_Y 236
#define BUTTON_CALIB_APPLY_W 132
#define BUTTON_CALIB_APPLY_H 36

#define BUTTON_CALIB_EXIT_X MARGIN
#define BUTTON_CALIB_EXIT_Y 236
#define BUTTON_CALIB_EXIT_W 132
#define BUTTON_CALIB_EXIT_H 36

// Offset calibration buttons - repositioned for Step 1/5 layout
#define BUTTON_CALIB_OFFSET_X (UI_W - MARGIN - 132)
#define BUTTON_CALIB_OFFSET_Y 236
#define BUTTON_CALIB_OFFSET_W 132
#define BUTTON_CALIB_OFFSET_H 36

// Record button - moved to same position as Calibrate button
#define BUTTON_CALIB_RECORD_X (UI_W - MARGIN - 132)
#define BUTTON_CALIB_RECORD_Y 236
#define BUTTON_CALIB_RECORD_W 132
#define BUTTON_CALIB_RECORD_H 36

// Battery view buttons
#define BATTERY_BUTTON_H 40
#define BATTERY_BUTTON_Y (UI_H - NAV_H - BATTERY_BUTTON_H - GAP)

// Exit button for Step 1/5 - lower left
#define BUTTON_CALIB_EXIT_OFFSET_X MARGIN
#define BUTTON_CALIB_EXIT_OFFSET_Y 236
#define BUTTON_CALIB_EXIT_OFFSET_W 132
#define BUTTON_CALIB_EXIT_OFFSET_H 36

// Skip SG Calibration buttons
#define BUTTON_CALIB_SKIP_X MARGIN
#define BUTTON_CALIB_SKIP_Y 236
#define BUTTON_CALIB_SKIP_W 132
#define BUTTON_CALIB_SKIP_H 36

// Skip confirmation buttons - repositioned to avoid conflicts
#define BUTTON_CALIB_SKIP_YES_X (UI_W - MARGIN - 132)
#define BUTTON_CALIB_SKIP_YES_Y 236
#define BUTTON_CALIB_SKIP_YES_W 132
#define BUTTON_CALIB_SKIP_YES_H 36

#define BUTTON_CALIB_SKIP_NO_X MARGIN
#define BUTTON_CALIB_SKIP_NO_Y 236
#define BUTTON_CALIB_SKIP_NO_W 132
#define BUTTON_CALIB_SKIP_NO_H 36

// Function prototypes
void initESPNow();
void initDisplay();
void initTouch();
void initRTC();
void syncSystemTimeFromRTC(uint32_t epoch);
bool readRTCDateTime(uint16_t* year, uint8_t* month, uint8_t* day,
                     uint8_t* hour, uint8_t* minute, uint8_t* second);
bool setRTCDateTime(uint16_t year, uint8_t month, uint8_t day,
                    uint8_t hour, uint8_t minute, uint8_t second);
uint32_t getCurrentEpoch();
bool isEpochValid(uint32_t epoch);
void formatTimestamp(uint32_t epoch, char* buf, size_t bufSize);
uint32_t buildEpochWithUploadOffset();
uint32_t parseDateTimeToEpoch(const char* timestamp);
void onDataReceived(const uint8_t *mac, const uint8_t *incomingData, int len);
void onPlugStatusReceived(const uint8_t *mac, const uint8_t *incomingData, int len);
void sendPlugCommandIfDue();
bool hasValidPlugBeerTemperature();
float currentPlugBeerTemperatureC();
bool hasValidPlugAirTemperature();
bool hasFreshPlugStatus();
bool usesPlugTemperatureAsPrimary();
bool isPostPackageTemperaturePhase();
bool isFloatInactiveAfterPackaging();
bool shouldShowFloatStillActiveWarning();
float effectiveTemperatureC(float floatTemperatureC);
float latestDisplayedTemperatureC();
bool ensureFloatPeerRegistered(const uint8_t* mac);
void setFloatZeroCalStatus(const char* message);
void sendDataAck(const uint8_t* mac, const payload_t& data);
bool isDuplicateFloatSequence(uint16_t sequence_id);
void rememberFloatSequence(uint16_t sequence_id);
void onCalibrationResponse(const uint8_t *mac, const uint8_t *incomingData, int len);
void onCalibrationCommandFromFloat(const uint8_t *mac, const uint8_t *incomingData, int len);
void onCalibrationCoefficients(const uint8_t *mac, const uint8_t *incomingData, int len);
void drawLiveView();
void drawFloatOffAngleTile(int x, int y, int w, int h);
void drawGraphView();
void drawCalibrationView();
void drawBatteryView();
void drawMoreView();
void drawLiveDetailsView();
void drawPolynomialGraph();
void drawTempGraphView();
void drawTempGraphModeToggle(int contentY);
void drawAngleGraphView();
void drawAbvGraphView();
void drawBrewWizardScreen();
void drawOGVerificationScreen();
void drawTargetVsActualChart();
float targetChartHours();
float temperatureChartHours();
float postPackageTemperatureChartHours();
uint32_t postPackageTemperatureStartEpoch();
float postPackageTemperatureStartHour();
float targetStartOffsetHours();
unsigned long fermentationElapsedSecondsAt(unsigned long epoch);
float targetModelHourForChartHour(float chartHour);
float targetChartHourForModelHour(float modelHour);
float expectedTargetSGAtChartHour(float chartHour);
float currentTemperatureTargetC(unsigned long nowEpoch);
TemperatureProfileRuntimePhase currentTemperaturePhase(unsigned long nowEpoch);
float currentTemperatureRampKPerHour(unsigned long nowEpoch);
const char* currentDisplayPhaseName(unsigned long nowEpoch);
void loadPlugTestScheduleIfNeeded();
float plugTestScheduleTargetC(float fallbackTarget, unsigned long nowEpoch);
float targetHourForSG(float targetSG, float chartHours);
float targetHourForAttenuation(float attenuationPercent, float chartHours);
float eventHourFromEpoch(unsigned long eventEpoch);
int graphXForHour(float hour, int graphX, int graphW, float chartHours);
float pointHourForBatchChart(int pointIndex);
void drawTargetEventMarker(int gx, int gy, int gw, int gh, float chartHours,
                           float hour, const char* label, uint16_t color, int labelSlot, int labelSide);
void drawTargetChartSpanLabel(int gx, int gy, int gw, float chartHours,
                              float startHour, float endHour, const char* label, uint16_t color, int row);
void drawTargetChartEventMarkers(int gx, int gy, int gw, int gh, float chartHours, bool includePostPackage = true);
void drawPostPackageTemperatureEventMarkers(int gx, int gy, int gw, int gh, float chartHours);
void drawTargetChartXAxis(int gx, int gy, int gw, int gh, float chartHours);
void drawDashboardScreen();
void drawNewYeastScreen();
void drawManageYeastScreen();
void drawManageBrewScreen();
void drawRecommendationPanel(int x, int y, int w, int h);
void calculateGraphPoints();
void drawGraphAxes();
void drawGraphCurve();
void checkTouch();
float calculateGravity(float tilt);

void addDataPoint(payload_t data, uint32_t epoch_s);
void drawGrid();
void drawGraph();
void loadFloatMacFromEEPROM();
void saveFloatMacToEEPROM();
void loadPlugMacFromEEPROM();
void savePlugMacToEEPROM();
void startWait(int durationMs);
void checkWaitTimeout();
void stopWait();
void sendCalibrationCommand(uint8_t command, float target_sg);
void applyCalibration();
int calibrationPointCount();
int calibrationPointIndex(CalibMode mode);
CalibMode calibrationModeForPoint(int index);
float calibrationTargetSG(int index);
int calibrationAddAmount(int index);
void sendExitCalibrationCommand();
void abortCalibrationFlow();
bool logDataToSD(payload_t data, uint32_t epoch_s);
void logPostPackagingTemperatureIfDue();
void createNewFermentationFile();
bool ensureFermentationLogFile(const char* batchId);
bool createFreshBatchLogFile(const char* batchId);
void rollbackBatchFiles(const char* batchId);
bool findBestFallbackBatch(char* batchId, size_t bufferSize);
void drawCreateNewDialog();
void checkExistingFermentation();
bool loadHistoricalDataFromCSV(const char* filename, 
                               GraphLoadMode mode = LOAD_6H,
                               int maxPoints = MAX_DATA_POINTS,
                               int samplingStep = 1);
bool parseCSVDataLine(const char* line, payload_t* data, uint32_t* epoch_s, uint8_t* battery_percent);
bool isPostPackageCsvTemperaturePoint(const payload_t& data, uint32_t epoch_s);
void clearPostPackageTemperatureGraphData();
void appendPostPackageTemperatureGraphData(uint32_t epoch_s, float temperatureC);
bool loadPostPackageTemperatureGraphData();
void checkOGStability(float currentSG);
void logOGToSD();
float calculateABV(float og, float currentSG);
bool isPlausibleSensorReading(const payload_t& data, const char** issue);
void beginBrewWizard();
void completeBrewWizard();
void cancelBrewWizard();
void beginNewYeastWizard(const char* presetId = NULL);
void loadYeastStepBuffer();
void commitYeastStepBuffer();
void drawNewYeastNav(const char* nextLabel);
bool handleNewYeastTouch(int x, int y);
void saveNewYeastWizard();
void loadManagedYeasts();
bool handleManageYeastTouch(int x, int y);
void loadManagedBatches();
bool handleManageBrewTouch(int x, int y);
void updateFermentationAssistant(payload_t data, uint32_t epoch_s);
void refreshFermentationAssistantFromProfile();
float smoothedGravityDeltaPerHour(int maxReadings);
bool migrateActiveBrewProfileFromHistory(const char* logPath);
void finalizeHistoricalDataLoad();
void markScreenDirtyForFloatData();
void clearHistoricalDisplayData();
void clearBufferedSensorData();
bool shouldRecordBatchFloatData();
void drawWrappedText(int x, int y, int w, const char* text, uint16_t color);
void persistActiveBrewProfile();
void startNewBatchStorage(const char* batchId);
void formatDurationShort(unsigned long seconds, char* buffer, size_t bufferSize);
void handleOGChoice(bool useMeasuredOG);
void saveYeastPerformanceSummary(float finalGravity, uint32_t completedAt);
void refreshCurrentBatchAction(float currentSG, unsigned long nowEpoch);
bool autoStartColdCrashIfPlugReady(unsigned long nowEpoch);
BatchAction evaluateBatchActionWithHysteresis(FermentationPhase phase, float attenuation,
                                              float currentSG, float gravityDeltaPerHour,
                                              unsigned long nowEpoch);
bool shouldKeepDryHopActionLatched(const BatchAction& previousAction,
                                   const BatchAction& nextAction,
                                   float currentSG, float gravityDeltaPerHour);
BatchAction makeLatchedDryHopAction(float currentSG);
void handleCurrentActionChoice(bool done);
void formatActionHeader(char* buffer, size_t bufferSize);
uint8_t calculateBatteryPercentage(float voltage);
bool getLatestDisplayBatteryVoltage(float* voltageOut);
void updateChargingState(float currentVoltage);
float calculateDischargeRateLinearRegression();

// Graph cursor helper functions
void formatTimeFromDataPoint(int index, char* buf, int bufSize);
void updateCursorPosition();
void drawCursorValueDisplay(int x, int y, bool showRight);

// View helper functions
void drawViewTopbar(const char* title);
void drawSdWarningTopbar();
bool shouldShowSdWarning();
void loadAllHistoryForDetailChart();
void drawNoDataCard(const char* message, const char* subtext, int activeTab);
void drawDetailSection(int* y, const char* title);
void drawDetailRow(int* y, const char* label, const char* value);
void drawDetailSectionAt(int x, int* y, int w, const char* title);
void drawDetailRowAt(int x, int* y, int w, const char* label, const char* value);
void resetPlugGovernorSettingsToDefaults();
bool ensurePlugGovernorSettingsLoaded();
bool savePlugGovernorSettingsToSD();
void drawPlugGovernorView();
bool handleLiveDetailsTouch(int x, int y);
bool handlePlugGovernorTouch(int x, int y);

// Graph button handler functions
void handleGraphButton6h();
void handleGraphButton24h();
void handleGraphButtonAll();
void handleGraphButtonLeft();
void handleGraphButtonRight();
#if SGNODE_BATTERY_DEBUG
void handleBatteryDebugSerial();
#endif

// Time-based SPI separation functions
bool mountSDTemporarily();
void dismountSD();
void bufferSensorData(payload_t data, uint32_t epoch_s);
void writeBufferedDataToSD();
bool isSafeForSDOperation();

// UI Design System Helper Functions
void drawButton(int x, int y, int w, int h, const char* label, bool active);
void drawThemeToggle(int x, int y, bool enabled);
bool isLogoBackgroundPixel(uint16_t color);
void toggleTheme();
void loadThemePreference();
void saveThemePreference();
void initBacklight();
void applyBacklightLevel();
void cycleBacklightLevel();
void loadBacklightPreference();
void saveBacklightPreference();
void startBaseOtaMode();
void handleBaseOtaMode();
void stopBaseOtaAndReboot();
void drawBaseOtaScreen();
void drawBaseOtaConfirmDialog();
void drawFloatOtaPopup();
void drawTopbarPulldown();
bool handleOverlayTouch(int x, int y);
void onFloatOtaStatusReceived(const uint8_t* mac, const uint8_t* data, int len);
void drawBootScreen();
void uiInitColors();
void drawCurrentScreen();

void setup() {
  Serial.begin(115200);
  LOG_INFOLN("=== SGNode Base Station alpha 0.5.0 starting ===");
  
  loadThemePreference();
  loadBacklightPreference();
  #if SGNODE_UI_TEST_HARNESS
    // Keep harness sessions visually stable and clearly readable.
    darkMode = true;
  #endif
  
  // Initialize UI color tokens from theme
  uiInitColors();
  
  initDisplay();
  initBacklight();
  initTouch();
  initCalibration();
  initRTC();
  
  // Initialize SD CS pin but don't mount SD yet (to avoid touch interference)
  #if SD_ENABLED
    pinMode(SD_CS, OUTPUT);
    digitalWrite(SD_CS, HIGH); // Ensure SD CS is HIGH initially
    LOG_INFOLN("SD card CS pin initialized (not mounted yet)");
    LOG_INFOLN("Touch ready - SD will mount temporarily when needed");
  #else
    LOG_INFOLN("SD card DISABLED");
  #endif
  
  initESPNow();
  
  // Load float MAC from EEPROM for permanent pairing
  loadFloatMacFromEEPROM();
  loadPlugMacFromEEPROM();
  
  // Show boot screen first
  drawBootScreen();
  
  // Check for existing fermentation and auto-continue or create new
  checkExistingFermentation();
  
  LOG_INFOLN("Base station ready");
  // Initial screen draw happens through the normal dirty-screen path so
  // restored historical data and the selected view use the same refresh logic.
  screenDirty = true;
  staticElementsDrawn = false;
  #if SGNODE_UI_TEST_HARNESS
    topbarDirty = true;
  #endif
}

void loop() {
  if (baseOtaActive) {
    if (millis() - lastTouchCheck > TOUCH_CHECK_INTERVAL) {
      checkTouch();
      lastTouchCheck = millis();
    }
    handleBaseOtaMode();
    delay(5);
    return;
  }

  #if SGNODE_UI_TEST_HARNESS
    handleUITestHarness();
  #endif
  #if SGNODE_BATTERY_DEBUG
    handleBatteryDebugSerial();
  #endif

  sendPlugCommandIfDue();

  // Check for touch input
  if (millis() - lastTouchCheck > TOUCH_CHECK_INTERVAL) {
    checkTouch();
    lastTouchCheck = millis();
  }
  
  // Check wait timeout for calibration
  checkWaitTimeout();

  if (millis() - lastTopbarRefresh >= TOPBAR_REFRESH_INTERVAL) {
    topbarDirty = true;
    lastTopbarRefresh = millis();
  }
  
  // Check if it's safe to perform SD operations (no recent touch activity)
  if (isSafeForSDOperation() && (millis() - lastSDWrite) > SD_WRITE_INTERVAL) {
    writeBufferedDataToSD();
    lastSDWrite = millis();
  }

  logPostPackagingTemperatureIfDue();
  
  // Update display only when screen is dirty
  if (screenDirty) {
    drawCurrentScreen();
    screenDirty = false;
  } else {
    // Update topbar periodically so date/time and status stay current.
    if (topbarDirty) {
      uint8_t battPercent = 0;
      float latestVoltage = 0.0f;
      if (getLatestDisplayBatteryVoltage(&latestVoltage)) {
        battPercent = calculateBatteryPercentage(latestVoltage);
      }
      
      // Update topbar with appropriate title for current view
      const char* title = "Live";
      switch (currentMode) {
        case LIVE_VIEW:
          title = "Live";
          if (displayDataCount > 0) updateLiveViewDynamic();
          break;
        case GRAPH_VIEW:
          title = "Graph";
          break;
        case CALIBRATION_VIEW:
          title = "Calib";
          break;
        case BATTERY_VIEW:
          title = "Battery";
          break;
        case MORE_VIEW:
          title = "More";
          break;
        case POLY_GRAPH_VIEW:
          title = "Polynomial";
          break;
        case LIVE_DETAILS_VIEW:
          title = "Diagnostic";
          break;
        case TEMP_GRAPH_VIEW:
          title = "Temp";
          break;
        case ANGLE_GRAPH_VIEW:
          title = "Angle";
          break;
        case ABV_GRAPH_VIEW:
          title = "ABV";
          break;
        case BREW_WIZARD_VIEW:
          title = "Wizard";
          break;
        case OG_VERIFICATION_VIEW:
          title = "OG Verify";
          break;
        case TARGET_CHART_VIEW:
          title = "Target";
          break;
        case DASHBOARD_VIEW:
          title = "Dashboard";
          break;
        case NEW_YEAST_VIEW:
          title = "New Yeast";
          break;
        case MANAGE_YEAST_VIEW:
          title = "Manage Yeast";
          break;
        case MANAGE_BREW_VIEW:
          title = "Manage Brew";
          break;
        case PLUG_GOVERNOR_VIEW:
          title = "Plug Setup";
          break;
      }
      
      uiDrawTopbar(title, true, fermentationFileOpen, battPercent);
      drawSdWarningTopbar();
      topbarDirty = false;
    }
  }
  
  delay(10);
}

uint8_t bcdToDec(uint8_t value) {
  return ((value >> 4) * 10) + (value & 0x0F);
}

uint8_t decToBcd(uint8_t value) {
  return ((value / 10) << 4) | (value % 10);
}

int64_t daysFromCivil(int year, unsigned month, unsigned day) {
  year -= month <= 2;
  const int era = (year >= 0 ? year : year - 399) / 400;
  const unsigned yoe = (unsigned)(year - era * 400);
  const unsigned doy = (153 * (month + (month > 2 ? -3 : 9)) + 2) / 5 + day - 1;
  const unsigned doe = yoe * 365 + yoe / 4 - yoe / 100 + doy;
  return era * 146097 + (int)doe - 719468;
}

uint32_t dateTimeToEpoch(uint16_t year, uint8_t month, uint8_t day,
                         uint8_t hour, uint8_t minute, uint8_t second) {
  int64_t days = daysFromCivil(year, month, day);
  if (days < 0) return 0;
  return (uint32_t)(days * 86400 + (uint32_t)hour * 3600 + (uint32_t)minute * 60 + second);
}

void civilFromDays(int64_t z, uint16_t* year, uint8_t* month, uint8_t* day) {
  z += 719468;
  const int era = (z >= 0 ? z : z - 146096) / 146097;
  const unsigned doe = (unsigned)(z - era * 146097);
  const unsigned yoe = (doe - doe / 1460 + doe / 36524 - doe / 146096) / 365;
  int y = (int)yoe + era * 400;
  const unsigned doy = doe - (365 * yoe + yoe / 4 - yoe / 100);
  const unsigned mp = (5 * doy + 2) / 153;
  const unsigned d = doy - (153 * mp + 2) / 5 + 1;
  const unsigned m = mp + (mp < 10 ? 3 : -9);
  y += (m <= 2);
  *year = (uint16_t)y;
  *month = (uint8_t)m;
  *day = (uint8_t)d;
}

void epochToDateTime(uint32_t epoch, uint16_t* year, uint8_t* month, uint8_t* day,
                     uint8_t* hour, uint8_t* minute, uint8_t* second) {
  uint32_t secondsOfDay = epoch % 86400UL;
  civilFromDays(epoch / 86400UL, year, month, day);
  *hour = secondsOfDay / 3600UL;
  *minute = (secondsOfDay % 3600UL) / 60UL;
  *second = secondsOfDay % 60UL;
}

bool isEpochValid(uint32_t epoch) {
  return epoch >= dateTimeToEpoch(RTC_VALID_FROM_YEAR, 1, 1, 0, 0, 0);
}

uint8_t compileMonthNumber(const char* monthName) {
  static const char* months = "JanFebMarAprMayJunJulAugSepOctNovDec";
  const char* found = strstr(months, monthName);
  if (!found) return 1;
  return ((found - months) / 3) + 1;
}

uint32_t buildEpochWithUploadOffset() {
  char monthName[4] = {0};
  int day = 1;
  int year = 2024;
  int hour = 0;
  int minute = 0;
  int second = 0;
  sscanf(__DATE__, "%3s %d %d", monthName, &day, &year);
  sscanf(__TIME__, "%d:%d:%d", &hour, &minute, &second);
  return dateTimeToEpoch(year, compileMonthNumber(monthName), day, hour, minute, second) +
         RTC_COMPILE_UPLOAD_OFFSET_S;
}

bool readRTCDateTime(uint16_t* year, uint8_t* month, uint8_t* day,
                     uint8_t* hour, uint8_t* minute, uint8_t* second) {
  Wire.beginTransmission(RTC_I2C_ADDR);
  Wire.write(0x00);
  if (Wire.endTransmission() != 0) {
    return false;
  }
  
  if (Wire.requestFrom(RTC_I2C_ADDR, 7) != 7) {
    return false;
  }
  
  *second = bcdToDec(Wire.read() & 0x7F);
  *minute = bcdToDec(Wire.read() & 0x7F);
  uint8_t hourReg = Wire.read();
  if (hourReg & 0x40) {
    *hour = bcdToDec(hourReg & 0x1F);
    if (hourReg & 0x20) *hour = (*hour % 12) + 12;
  } else {
    *hour = bcdToDec(hourReg & 0x3F);
  }
  Wire.read(); // day-of-week
  *day = bcdToDec(Wire.read() & 0x3F);
  *month = bcdToDec(Wire.read() & 0x1F);
  *year = 2000 + bcdToDec(Wire.read());
  
  return *month >= 1 && *month <= 12 && *day >= 1 && *day <= 31 &&
         *hour <= 23 && *minute <= 59 && *second <= 59;
}

bool setRTCDateTime(uint16_t year, uint8_t month, uint8_t day,
                    uint8_t hour, uint8_t minute, uint8_t second) {
  Wire.beginTransmission(RTC_I2C_ADDR);
  Wire.write(0x00);
  Wire.write(decToBcd(second));
  Wire.write(decToBcd(minute));
  Wire.write(decToBcd(hour));
  Wire.write(decToBcd(1)); // day-of-week is not used by SGNode
  Wire.write(decToBcd(day));
  Wire.write(decToBcd(month));
  Wire.write(decToBcd(year >= 2000 ? year - 2000 : 0));
  if (Wire.endTransmission() != 0) {
    return false;
  }
  
  Wire.beginTransmission(RTC_I2C_ADDR);
  Wire.write(0x0F);
  Wire.write(0x00); // clear oscillator-stop flag on DS323x-compatible RTCs
  Wire.endTransmission();
  return true;
}

uint32_t getCurrentEpoch() {
  uint16_t year;
  uint8_t month, day, hour, minute, second;
  if (!readRTCDateTime(&year, &month, &day, &hour, &minute, &second)) {
    return 0;
  }
  return dateTimeToEpoch(year, month, day, hour, minute, second);
}

void formatTimestamp(uint32_t epoch, char* buf, size_t bufSize) {
  if (!isEpochValid(epoch)) {
    snprintf(buf, bufSize, "RTC_UNSET");
    return;
  }
  
  uint16_t year;
  uint8_t month, day, hour, minute, second;
  epochToDateTime(epoch, &year, &month, &day, &hour, &minute, &second);
  snprintf(buf, bufSize, "%04u-%02u-%02u %02u:%02u:%02u",
           year, month, day, hour, minute, second);
}

uint32_t parseDateTimeToEpoch(const char* timestamp) {
  int year, month, day, hour, minute, second;
  if (sscanf(timestamp, "%d-%d-%d %d:%d:%d", &year, &month, &day, &hour, &minute, &second) == 6) {
    return dateTimeToEpoch(year, month, day, hour, minute, second);
  }
  return 0;
}

void syncSystemTimeFromRTC(uint32_t epoch) {
  if (!isEpochValid(epoch)) return;
  timeval tv;
  tv.tv_sec = epoch;
  tv.tv_usec = 0;
  settimeofday(&tv, NULL);
}

void initRTC() {
  Wire.begin(RTC_SDA_PIN, RTC_SCL_PIN);
  
  uint32_t buildEpoch = buildEpochWithUploadOffset();
  uint32_t rtcEpoch = getCurrentEpoch();
  
  if (!isEpochValid(rtcEpoch) || rtcEpoch < buildEpoch) {
    uint16_t year;
    uint8_t month, day, hour, minute, second;
    epochToDateTime(buildEpoch, &year, &month, &day, &hour, &minute, &second);
    if (setRTCDateTime(year, month, day, hour, minute, second)) {
      syncSystemTimeFromRTC(buildEpoch);
      char ts[24];
      formatTimestamp(buildEpoch, ts, sizeof(ts));
      LOG_INFO("RTC set from compile time (+%ds): %s\n", RTC_COMPILE_UPLOAD_OFFSET_S, ts);
    } else {
      LOG_ERRORLN("RTC not found on SDA=32/SCL=25 (address 0x68)");
    }
  } else {
    syncSystemTimeFromRTC(rtcEpoch);
    char ts[24];
    formatTimestamp(rtcEpoch, ts, sizeof(ts));
    LOG_INFO("RTC running: %s\n", ts);
  }
}

void initESPNow() {
  // Set device as a Wi-Fi Station
  WiFi.mode(WIFI_STA);
  
  // Wait a moment for WiFi to fully initialize
  delay(500);
  
  // esp_wifi_set_channel is deprecated in newer ESP-IDF versions
  // ESP-NOW will automatically use the current WiFi channel
  
  // Initialize ESP-NOW
  if (esp_now_init() != ESP_OK) {
    LOG_ERRORLN("Error initializing ESP-NOW");
    return;
  }
  
  // Register receive callback (new ESP-IDF signature)
  esp_now_register_recv_cb([](const esp_now_recv_info_t *recv_info, const uint8_t *data, int len) {
    // Capture RSSI from received packet
    if (recv_info->rx_ctrl != NULL) {
      lastRSSI = recv_info->rx_ctrl->rssi;
      rssiAvailable = true;
    }
    
    // Typed Plug packets are dispatched before legacy size-based Float packets.
    if ((len == sizeof(sg_plug_status_t) || len == sizeof(sg_plug_status_v2_t)) &&
        data[0] == SG_PLUG_STATUS_TYPE) {
      onPlugStatusReceived(recv_info->src_addr, data, len);
    } else if (len == sizeof(sg_float_ota_status_t) && data[0] == SG_FLOAT_OTA_STATUS_TYPE) {
      onFloatOtaStatusReceived(recv_info->src_addr, data, len);
    } else if (len == sizeof(calib_response_t)) { // 42 bytes - Calibration response
      onCalibrationResponse(recv_info->src_addr, data, len);
    } else if (len == sizeof(calib_coeffs_t)) { // 26 bytes - Calibration coefficients
      // Check first byte to distinguish from sensor data
      if (len >= 1 && data[0] == 3) { // response_type = 3 for coefficients
        onCalibrationCoefficients(recv_info->src_addr, data, len);
      } else {
        onDataReceived(recv_info->src_addr, data, len); // Regular sensor data
      }
    } else if (len == sizeof(calib_command_t)) { // 6 bytes - Calibration command from float
      onCalibrationCommandFromFloat(recv_info->src_addr, data, len);
    } else if (len == sizeof(payload_t)) { // 26 bytes - Regular sensor data (fallback)
      onDataReceived(recv_info->src_addr, data, len);
    } else {
      LOG_ERROR("Unknown packet size: %d bytes\n", len);
    }
  });
  
  LOG_INFOLN("ESP-NOW initialized");
  
  // Print base station MAC address after WiFi is fully initialized
  String macAddress = WiFi.macAddress();
  LOG_INFO("Base Station MAC: %s\n", macAddress.c_str());
}

void setFloatZeroCalStatus(const char* message) {
  if (!message || message[0] == '\0') return;

  strncpy(floatZeroCalStatus, message, sizeof(floatZeroCalStatus) - 1);
  floatZeroCalStatus[sizeof(floatZeroCalStatus) - 1] = '\0';
  screenDirty = true;
}

void sendDataAck(const uint8_t* mac, const payload_t& data) {
  if (!mac) return;

  ack_packet_t ack;
  ack.packet_type = ACK_PACKET_TYPE;
  ack.sequence_id = data.sequence_id;
  ack.highest_seen = highestSeenFloatSeq;
  ack.command = SG_ACK_COMMAND_NONE;
  ack.command_id = floatZeroCalCommandId;

  bool zeroCalResult =
    (data.flags & (SG_PAYLOAD_FLAG_ZERO_CAL_OK | SG_PAYLOAD_FLAG_ZERO_CAL_FAIL)) != 0;
  if ((floatZeroCalCommandPending || floatZeroCalAwaitingConfirmation) && !zeroCalResult) {
    ack.command = SG_ACK_COMMAND_ZERO_CALIBRATE;
    ack.command_id = ++floatZeroCalCommandId;
  }

  if (!ensureFloatPeerRegistered(mac)) {
    if (ack.command == SG_ACK_COMMAND_ZERO_CALIBRATE) {
      setFloatZeroCalStatus("Zero ACK peer error");
    }
    return;
  }

  esp_err_t result = esp_now_send(mac, (uint8_t*)&ack, sizeof(ack));
  if (result == ESP_OK) {
    lastAckedFloatSeq = data.sequence_id;
    if (ack.command == SG_ACK_COMMAND_ZERO_CALIBRATE) {
      floatZeroCalCommandPending = false;
      floatZeroCalAwaitingConfirmation = true;
      char msg[80];
      snprintf(msg, sizeof(msg), "Zero ACK sent seq %u", data.sequence_id);
      setFloatZeroCalStatus(msg);
      LOG_INFO("Sent float zero calibration command id=%u at angle %.2f\n",
               ack.command_id, data.angle);
    }
  } else {
    if (ack.command == SG_ACK_COMMAND_ZERO_CALIBRATE) {
      char msg[80];
      snprintf(msg, sizeof(msg), "Zero ACK send failed %d", result);
      setFloatZeroCalStatus(msg);
    }
    LOG_VERBOSE("Failed to send ACK for seq=%u result=%d\n", data.sequence_id, result);
  }
}

bool isDuplicateFloatSequence(uint16_t sequence_id) {
  for (int i = 0; i < recentFloatSeqCount; i++) {
    if (recentFloatSeqs[i] == sequence_id) return true;
  }
  return false;
}

void rememberFloatSequence(uint16_t sequence_id) {
  recentFloatSeqs[recentFloatSeqIndex] = sequence_id;
  recentFloatSeqIndex = (recentFloatSeqIndex + 1) % 16;
  if (recentFloatSeqCount < 16) recentFloatSeqCount++;
  if (sequence_id > highestSeenFloatSeq || highestSeenFloatSeq == 0) {
    highestSeenFloatSeq = sequence_id;
  }
}

void initDisplay() {
  tft.init();
  tft.setRotation(1); // Landscape mode - MUST match touchCalibration_rotate in Touch.h (which is 1)
  
  // Verify screen dimensions after rotation
  LOG_INFO("Display dimensions after rotation: %dx%d\n", tft.width(), tft.height());
  
  tft.fillScreen(currentTheme->background);
  tft.setTextColor(currentTheme->textPrimary, currentTheme->background);
  
  LOG_INFOLN("Display initialized for 480x320 landscape (rotation 1)");
}

void drawCurrentScreen() {
  if (baseOtaActive) {
    drawBaseOtaScreen();
    return;
  }

  if (showingCreateNewDialog) {
    drawCreateNewDialog();
    return;
  }

  switch (currentMode) {
    case LIVE_VIEW:
      drawLiveView();
      break;
    case GRAPH_VIEW:
      drawGraphView();
      break;
    case CALIBRATION_VIEW:
      drawCalibrationView();
      break;
    case BATTERY_VIEW:
      drawBatteryView();
      break;
    case MORE_VIEW:
      drawMoreView();
      break;
    case POLY_GRAPH_VIEW:
      drawPolynomialGraph();
      break;
    case LIVE_DETAILS_VIEW:
      drawLiveDetailsView();
      break;
    case TEMP_GRAPH_VIEW:
      drawTempGraphView();
      break;
    case ANGLE_GRAPH_VIEW:
      drawAngleGraphView();
      break;
    case ABV_GRAPH_VIEW:
      drawAbvGraphView();
      break;
    case BREW_WIZARD_VIEW:
      drawBrewWizardScreen();
      break;
    case OG_VERIFICATION_VIEW:
      drawOGVerificationScreen();
      break;
    case TARGET_CHART_VIEW:
      drawTargetVsActualChart();
      break;
    case DASHBOARD_VIEW:
      drawDashboardScreen();
      break;
    case NEW_YEAST_VIEW:
      drawNewYeastScreen();
      break;
    case MANAGE_YEAST_VIEW:
      drawManageYeastScreen();
      break;
    case MANAGE_BREW_VIEW:
      drawManageBrewScreen();
      break;
    case PLUG_GOVERNOR_VIEW:
      drawPlugGovernorView();
      break;
  }

  if (baseOtaConfirmVisible) {
    drawBaseOtaConfirmDialog();
  }
  if (floatOtaPopupVisible) {
    drawFloatOtaPopup();
  }
  if (topbarPulldownVisible) {
    drawTopbarPulldown();
  }
}

void initTouch() {
  // TFT_eSPI touch is initialized automatically with tft.init()
  // Calibration values are set in User_Setup.h or Touch.h
  // Y-axis inversion now enabled in Touch.h (touchCalibration_invert_y = 1)
  
  // Ensure SD CS is HIGH to prevent SD card from interfering with touch
  pinMode(SD_CS, OUTPUT);
  digitalWrite(SD_CS, HIGH);
  
  LOG_INFOLN("Touch screen ready (using TFT_eSPI built-in support)");
}

bool ensureFloatPeerRegistered(const uint8_t* mac) {
  if (!mac) return false;

  if (!floatMacKnown || memcmp(floatMac, mac, sizeof(floatMac)) != 0) {
    memcpy(floatMac, mac, sizeof(floatMac));
    floatMacKnown = true;
    saveFloatMacToEEPROM();
  }

  if (esp_now_is_peer_exist(mac)) {
    return true;
  }

  esp_now_peer_info_t peerInfo = {};
  memcpy(peerInfo.peer_addr, mac, 6);
  peerInfo.channel = ESPNOW_CHANNEL;
  peerInfo.encrypt = false;
  peerInfo.ifidx = WIFI_IF_STA;

  esp_err_t addResult = esp_now_add_peer(&peerInfo);
  if (addResult == ESP_OK || addResult == ESP_ERR_ESPNOW_EXIST) {
    return true;
  }

  LOG_ERROR("Failed to register float as peer: %d\n", addResult);
  return false;
}

void onPlugStatusReceived(const uint8_t *mac, const uint8_t *incomingData, int len) {
  if (!mac || !incomingData ||
      (len != sizeof(sg_plug_status_t) && len != sizeof(sg_plug_status_v2_t))) return;

  sg_plug_status_t status = {};
  float pOffsetC = NAN;
  float iOffsetC = NAN;
  float dOffsetC = NAN;
  float rampTrimC = NAN;
  float rampITrimC = NAN;
  float rampRateErrorKPerHour = NAN;
  float beerRateRawCPerHour = NAN;
  bool componentsValid = false;

  if (len == sizeof(sg_plug_status_v2_t)) {
    sg_plug_status_v2_t statusV2;
    memcpy(&statusV2, incomingData, sizeof(statusV2));
    uint16_t calculatedCrc = sg_crc16((const uint8_t*)&statusV2, offsetof(sg_plug_status_v2_t, crc));
    if (statusV2.packet_type != SG_PLUG_STATUS_TYPE ||
        statusV2.version != SG_PROTOCOL_VERSION || statusV2.crc != calculatedCrc) {
      LOG_ERRORLN("Rejected invalid SGNode Plug status packet");
      return;
    }
    memcpy(&status, &statusV2, offsetof(sg_plug_status_t, crc));
    status.crc = statusV2.crc;
    pOffsetC = statusV2.p_offset_c;
    iOffsetC = statusV2.i_offset_c;
    dOffsetC = statusV2.d_offset_c;
    rampTrimC = statusV2.ramp_trim_c;
    rampITrimC = statusV2.ramp_i_offset_c;
    rampRateErrorKPerHour = statusV2.ramp_rate_error_k_per_h;
    beerRateRawCPerHour = statusV2.beer_rate_raw_c_per_h;
    componentsValid = isfinite(pOffsetC) && isfinite(iOffsetC) && isfinite(dOffsetC) &&
                      isfinite(rampTrimC) && isfinite(rampITrimC) &&
                      isfinite(rampRateErrorKPerHour) && isfinite(beerRateRawCPerHour);
  } else {
    memcpy(&status, incomingData, sizeof(status));
    uint16_t calculatedCrc = sg_crc16((const uint8_t*)&status, offsetof(sg_plug_status_t, crc));
    if (status.packet_type != SG_PLUG_STATUS_TYPE ||
        status.version != SG_PROTOCOL_VERSION || status.crc != calculatedCrc) {
      LOG_ERRORLN("Rejected invalid SGNode Plug status packet");
      return;
    }
  }

  if (!plugMacKnown) {
    memcpy(plugMac, mac, sizeof(plugMac));
    plugMacKnown = true;
    savePlugMacToEEPROM();

    esp_now_peer_info_t peerInfo = {};
    memcpy(peerInfo.peer_addr, plugMac, sizeof(plugMac));
    peerInfo.channel = ESPNOW_CHANNEL;
    peerInfo.encrypt = false;
    peerInfo.ifidx = WIFI_IF_STA;
    esp_err_t addResult = esp_now_add_peer(&peerInfo);
    if (addResult != ESP_OK && addResult != ESP_ERR_ESPNOW_EXIST) {
      LOG_ERROR("Failed to register SGNode Plug peer: %d\n", addResult);
    }
  } else if (memcmp(plugMac, mac, sizeof(plugMac)) != 0) {
    LOG_ERRORLN("Ignored SGNode Plug status from unknown MAC");
    return;
  }

  bool beerTemperatureValid = (status.faults & SG_PLUG_FAULT_BEER_SENSOR) == 0 &&
    !isnan(status.beer_temp_c) && !isinf(status.beer_temp_c) &&
    status.beer_temp_c > -5.0f && status.beer_temp_c < 60.0f;

  latestPlugStatus = status;
  latestPlugStatusValid = true;
  latestPlugStatusMs = millis();
  latestPlugPComponentC = pOffsetC;
  latestPlugIComponentC = iOffsetC;
  latestPlugDComponentC = dOffsetC;
  latestPlugRampTrimC = rampTrimC;
  latestPlugRampITrimC = rampITrimC;
  latestPlugRampRateErrorKPerHour = rampRateErrorKPerHour;
  latestPlugBeerRateRawCPerHour = beerRateRawCPerHour;
  latestPlugComponentsValid = componentsValid;
  if (beerTemperatureValid) {
    lastValidPlugBeerTemperatureC = latestPlugStatus.beer_temp_c;
    plugBeerTemperatureMissCount = 0;
  } else if (plugBeerTemperatureMissCount < 255) {
    plugBeerTemperatureMissCount++;
  }
  tileTempDirty = true;
  topbarDirty = true;
  detailsDirty = true;
  screenDirty = true;
}

bool hasValidPlugBeerTemperature() {
  if (!latestPlugStatusValid || millis() - latestPlugStatusMs > 5UL * 60000UL) return false;
  bool directValid = (latestPlugStatus.faults & SG_PLUG_FAULT_BEER_SENSOR) == 0 &&
    !isnan(latestPlugStatus.beer_temp_c) && !isinf(latestPlugStatus.beer_temp_c) &&
    latestPlugStatus.beer_temp_c > -5.0f && latestPlugStatus.beer_temp_c < 60.0f;
  if (directValid) return true;
  return plugBeerTemperatureMissCount > 0 && plugBeerTemperatureMissCount <= 3 &&
         !isnan(lastValidPlugBeerTemperatureC) && !isinf(lastValidPlugBeerTemperatureC);
}

float currentPlugBeerTemperatureC() {
  if (!latestPlugStatusValid || millis() - latestPlugStatusMs > 5UL * 60000UL) return NAN;
  bool directValid = (latestPlugStatus.faults & SG_PLUG_FAULT_BEER_SENSOR) == 0 &&
    !isnan(latestPlugStatus.beer_temp_c) && !isinf(latestPlugStatus.beer_temp_c) &&
    latestPlugStatus.beer_temp_c > -5.0f && latestPlugStatus.beer_temp_c < 60.0f;
  if (directValid) return latestPlugStatus.beer_temp_c;
  if (plugBeerTemperatureMissCount > 0 && plugBeerTemperatureMissCount <= 3 &&
      !isnan(lastValidPlugBeerTemperatureC) && !isinf(lastValidPlugBeerTemperatureC)) {
    return lastValidPlugBeerTemperatureC;
  }
  return NAN;
}

bool hasValidPlugAirTemperature() {
  if (!latestPlugStatusValid || millis() - latestPlugStatusMs > 5UL * 60000UL) return false;
  if ((latestPlugStatus.faults & SG_PLUG_FAULT_AIR_SENSOR) != 0) return false;
  return !isnan(latestPlugStatus.air_temp_c) && !isinf(latestPlugStatus.air_temp_c) &&
         latestPlugStatus.air_temp_c > -20.0f && latestPlugStatus.air_temp_c < 60.0f;
}

bool hasFreshPlugStatus() {
  return latestPlugStatusValid && millis() - latestPlugStatusMs <= 5UL * 60000UL;
}

bool usesPlugTemperatureAsPrimary() {
  return brewProfileLoaded && activeBrewProfile.plugControlEnabled && !activeBrewProfile.completed;
}

bool isPostPackageTemperaturePhase() {
  return brewProfileLoaded &&
         (activeBrewProfile.packageStarted || activeBrewProfile.packageDone) &&
         !activeBrewProfile.packageSkipped &&
         !activeBrewProfile.completed;
}

bool isFloatInactiveAfterPackaging() {
  return isPostPackageTemperaturePhase();
}

bool shouldShowFloatStillActiveWarning() {
  return isFloatInactiveAfterPackaging() &&
         lastPostPackageFloatPacketMs > 0 &&
         millis() - lastPostPackageFloatPacketMs < 15UL * 60UL * 1000UL;
}

float effectiveTemperatureC(float floatTemperatureC) {
  if (isPostPackageTemperaturePhase()) {
    return hasValidPlugAirTemperature() ? latestPlugStatus.air_temp_c : NAN;
  }
  if (usesPlugTemperatureAsPrimary()) {
    float plugBeerC = currentPlugBeerTemperatureC();
    if (!isnan(plugBeerC) && !isinf(plugBeerC)) return plugBeerC;
  }
  float plugBeerC = currentPlugBeerTemperatureC();
  return !isnan(plugBeerC) && !isinf(plugBeerC) ? plugBeerC : floatTemperatureC;
}

float latestDisplayedTemperatureC() {
  if (isPostPackageTemperaturePhase()) {
    return hasValidPlugAirTemperature() ? latestPlugStatus.air_temp_c : NAN;
  }
  float plugBeerC = currentPlugBeerTemperatureC();
  if (!isnan(plugBeerC) && !isinf(plugBeerC)) return plugBeerC;
  return latestFloatDataValid ? latestFloatData.temperature : NAN;
}

void sendPlugCommandIfDue() {
  const uint32_t nowMs = millis();
  if (!plugMacKnown || nowMs - lastPlugCommandMs < 60000UL) return;
  lastPlugCommandMs = nowMs;
  ensurePlugGovernorSettingsLoaded();
  plugControllerKp = plugGovSettings.kp;
  plugControllerTnHours = plugGovSettings.integralTnHours;
  plugControllerDBrakeHours = plugGovSettings.dBrakeHours;

  sg_plug_command_t command = {};
  command.packet_type = SG_PLUG_COMMAND_TYPE;
  command.version = SG_PROTOCOL_VERSION;
  command.sequence_id = ++plugCommandSequence;
  command.base_epoch = getCurrentEpoch();
  command.beer_target_c = brewProfileLoaded ? currentTemperatureTargetC(command.base_epoch) : 20.0f;
  command.ramp_k_per_h = brewProfileLoaded ? currentTemperatureRampKPerHour(command.base_epoch) : 0.0f;
  float plugBeerC = currentPlugBeerTemperatureC();
  if (plugTestScheduleEnabled && plugTestStarted && !isnan(plugBeerC) && !isinf(plugBeerC)) {
    command.ramp_k_per_h = plugBeerC > command.beer_target_c + 0.3f ? 1.0f : 0.0f;
  }
  command.batch_liters = brewProfileLoaded ? activeBrewProfile.batchSizeLiters : 20.0f;
  command.controller_kp = plugControllerKp;
  command.controller_tn_h = plugControllerTnHours;
  command.controller_d_brake_h = plugControllerDBrakeHours;
  command.air_turn_off_above_target_c = plugGovSettings.airTurnOffAboveTargetC;
  command.air_turn_on_above_target_c = plugGovSettings.airTurnOnAboveTargetC;
  command.air_minimum_on_s = plugGovSettings.airMinimumOnS;
  command.air_minimum_off_s = plugGovSettings.airMinimumOffS;
  command.cold_integral_band_c = plugGovSettings.coldIntegralBandC;
  command.warm_integral_band_c = plugGovSettings.warmIntegralBandC;
  command.max_positive_integral_c = plugGovSettings.maxPositiveIntegralC;
  command.max_negative_integral_c = plugGovSettings.maxNegativeIntegralC;
  command.integral_leak_per_hour = plugGovSettings.integralLeakPerHour;
  command.error_crossing_keep_factor = plugGovSettings.errorCrossingKeepFactor;
  command.max_d_offset_c = plugGovSettings.maxDOffsetC;
  command.warming_d_factor = plugGovSettings.warmingDFactor;
  command.beer_undershoot_lockout_c = plugGovSettings.beerUndershootLockoutC;
  command.fast_warming_rate_k_per_h = plugGovSettings.fastWarmingRateKPerH;
  command.strong_undershoot_c = plugGovSettings.strongUndershootC;
  command.strong_undershoot_air_offset_c = plugGovSettings.strongUndershootAirOffsetC;
  command.min_air_target_c = plugGovSettings.minAirTargetC;
  command.max_air_target_c = plugGovSettings.maxAirTargetC;
  command.target_step_c = plugGovSettings.targetStepC;
  command.ramp_controller_kp_h = plugGovSettings.rampControllerKpHours;
  command.ramp_controller_tn_h = plugGovSettings.rampControllerTnHours;
  command.max_ramp_trim_c = plugGovSettings.maxRampTrimC;
  command.ramp_fade_distance_c = plugGovSettings.rampFadeDistanceC;
  command.rate_filter_samples = plugGovSettings.rateFilterSamples;
  command.flags = brewProfileLoaded && !activeBrewProfile.completed && activeBrewProfile.plugControlEnabled
    ? SG_PLUG_COMMAND_ENABLE
    : 0;
  command.crc = sg_crc16((const uint8_t*)&command, offsetof(sg_plug_command_t, crc));

  esp_err_t result = esp_now_send(plugMac, (uint8_t*)&command, sizeof(command));
  if (result != ESP_OK) {
    LOG_ERROR("Failed to send SGNode Plug command: %d\n", result);
  }
}

void onDataReceived(const uint8_t *mac, const uint8_t *incomingData, int len) {
  if (len == sizeof(payload_t)) {
    // Store float MAC address if not known yet
    if (!floatMacKnown) {
      memcpy(floatMac, mac, 6);
      floatMacKnown = true;
      LOG_INFO("Float MAC address captured: %02X:%02X:%02X:%02X:%02X:%02X\n", 
                    floatMac[0], floatMac[1], floatMac[2], floatMac[3], floatMac[4], floatMac[5]);
      
      // Save to EEPROM for permanent pairing
      saveFloatMacToEEPROM();
      
      // Register float as ESP-NOW peer for direct communication
      esp_now_peer_info_t peerInfo = {};
      memcpy(peerInfo.peer_addr, floatMac, 6);
      peerInfo.channel = ESPNOW_CHANNEL;
      peerInfo.encrypt = false;
      peerInfo.ifidx = WIFI_IF_STA;
      
      esp_err_t addResult = esp_now_add_peer(&peerInfo);
      if (addResult == ESP_OK) {
        LOG_INFOLN("Float unit registered as ESP-NOW peer");
      } else if (addResult == ESP_ERR_ESPNOW_EXIST) {
        LOG_INFOLN("Float unit already registered as peer");
      } else {
        LOG_ERROR("Failed to register float as peer: %d\n", addResult);
      }
    }
    
    payload_t receivedData;
    memcpy(&receivedData, incomingData, len);
    
    // Verify protocol version
    if (receivedData.version != SG_PROTOCOL_VERSION) {
      LOG_ERROR("Warning: Protocol version mismatch (expected %d, got %d)\n", SG_PROTOCOL_VERSION, receivedData.version);
      return;
    }
    
    // Verify CRC (exclude version field for backward compatibility)
    size_t payload_size = sizeof(receivedData) - sizeof(receivedData.crc) - sizeof(receivedData.version);
    uint16_t calculated_crc = 0xFFFF;
    for (size_t i = 0; i < payload_size; i++) {
      calculated_crc ^= ((uint8_t*)&receivedData)[i + sizeof(receivedData.version)];
      for (uint8_t j = 0; j < 8; j++) {
        calculated_crc = (calculated_crc >> 1) ^ (calculated_crc & 1 ? 0xA001 : 0);
      }
    }
    
    if (calculated_crc != receivedData.crc) {
      LOG_ERROR("CRC mismatch: expected %d, got %d\n", receivedData.crc, calculated_crc);
      return;
    }

    bool duplicatePacket = isDuplicateFloatSequence(receivedData.sequence_id);
    if (!duplicatePacket) {
      rememberFloatSequence(receivedData.sequence_id);
    } else {
      duplicateFloatPackets++;
    }
    sendDataAck(mac, receivedData);
    
    uint32_t receivedEpoch = getCurrentEpoch();

    payload_t normalizedData = receivedData;
    bool batteryPlausible = !isnan(receivedData.battery_voltage) &&
                            !isinf(receivedData.battery_voltage) &&
                            receivedData.battery_voltage >= 2.5f &&
                            receivedData.battery_voltage <= 4.4f;
    if (!batteryPlausible) {
      float fallbackVoltage = 0.0f;
      if (getLatestDisplayBatteryVoltage(&fallbackVoltage)) {
        normalizedData.battery_voltage = fallbackVoltage;
      } else {
        normalizedData.battery_voltage = 0.0f;
      }
      LOG_ERROR("Invalid battery sample %.2fV sanitized to %.2fV\n",
                receivedData.battery_voltage, normalizedData.battery_voltage);
    }

    bool ignoreFloatForBatch = isPostPackageTemperaturePhase();
    if (ignoreFloatForBatch) {
      lastPostPackageFloatPacketMs = millis();
      lastPostPackageFloatPacket = normalizedData;
      lastPostPackageFloatPacketEpoch = receivedEpoch;
      lastPostPackageFloatPacketValid = true;
      topbarDirty = true;
      detailsDirty = true;
      screenDirty = true;
    }
    if (!ignoreFloatForBatch) {
      latestFloatTemperatureC = receivedData.temperature;
      normalizedData.temperature = effectiveTemperatureC(receivedData.temperature);

      latestFloatData = normalizedData;
      latestFloatEpoch = receivedEpoch;
      latestFloatDataValid = true;
    }

    uint8_t batteryPercent = calculateBatteryPercentage(normalizedData.battery_voltage);

    if ((receivedData.flags & SG_PAYLOAD_FLAG_ZERO_CAL_OK) != 0 && brewProfileLoaded) {
      floatZeroCalCommandPending = false;
      floatZeroCalAwaitingConfirmation = false;
      activeBrewProfile.floatZeroCalDone = true;
      activeBrewProfile.floatZeroCalSkipped = false;
      activeBrewProfile.floatZeroCalibratedAt = receivedEpoch;
      if (mountSDTemporarily()) {
        BrewProfileStore::save(activeBrewProfile);
        BrewProfileStore::appendBatchEvent(activeBrewProfile.batchId, receivedEpoch,
                                           "FLOAT_ZERO_CAL_DONE",
                                           "Float zero calibration confirmed",
                                           normalizedData.angle);
        dismountSD();
      }
      currentRecommendation.code = 0;
      currentRecommendation.message[0] = '\0';
      currentBatchAction.type = ACTION_NONE;
      currentBatchAction.code = 0;
      currentBatchAction.message[0] = '\0';
      floatZeroCalStatus[0] = '\0';
      refreshFermentationAssistantFromProfile();
    } else if ((receivedData.flags & SG_PAYLOAD_FLAG_ZERO_CAL_FAIL) != 0 && brewProfileLoaded) {
      floatZeroCalCommandPending = false;
      floatZeroCalAwaitingConfirmation = false;
      activeBrewProfile.floatZeroCalDone = false;
      if (mountSDTemporarily()) {
        BrewProfileStore::save(activeBrewProfile);
        BrewProfileStore::appendBatchEvent(activeBrewProfile.batchId, receivedEpoch,
                                           "FLOAT_ZERO_CAL_FAILED",
                                           "Place float level and retry",
                                           normalizedData.angle);
        dismountSD();
      }
      currentRecommendation.code = 12;
      strncpy(currentRecommendation.message, "Zero calibration failed", sizeof(currentRecommendation.message) - 1);
      currentRecommendation.message[sizeof(currentRecommendation.message) - 1] = '\0';
    }
    
    // Update charging state only with plausible battery values
    if (batteryPlausible && !ignoreFloatForBatch) {
      updateChargingState(normalizedData.battery_voltage);
    }
    
    LOG_VERBOSE("Received: seq=%d, angle=%.2fÂ°, density=%.3f, temp=%.1fÂ°C, battery=%.2fV (%d%%) [%s]\n", 
                  normalizedData.sequence_id, normalizedData.angle, normalizedData.density,
                  normalizedData.temperature, normalizedData.battery_voltage, batteryPercent,
                  chargingState == CHARGING ? "CHARGING" : 
                  chargingState == DISCHARGING ? "DISCHARGING" : "UNKNOWN");
    
    if (!duplicatePacket) {
      if (ignoreFloatForBatch) {
        LOG_VERBOSE("Ignoring float packet seq=%u after packaging\n", receivedData.sequence_id);
        markScreenDirtyForFloatData();
        return;
      }

      bool recordBatchFloatData = shouldRecordBatchFloatData();

      // Check OG stability if not yet captured
      if (recordBatchFloatData && !brewProfileLoaded && !ogCaptured && fermentationFileOpen) {
        checkOGStability(normalizedData.density);
      }

      // Calculate ABV if OG is captured
      if (ogCaptured) {
        currentABV = calculateABV(originalGravity, normalizedData.density);
      }

      if (recordBatchFloatData) {
        updateFermentationAssistant(normalizedData, receivedEpoch);
      } else {
        refreshCurrentBatchAction(normalizedData.density, receivedEpoch);
      }

      // Add data to display buffer
      addDataPoint(normalizedData, receivedEpoch);

      // Buffer sensor data for SD writing only after the float is confirmed in the brew.
      if (recordBatchFloatData) {
        bufferSensorData(normalizedData, receivedEpoch);
      }
    } else {
      LOG_VERBOSE("Duplicate float packet seq=%u acknowledged, not logged again\n", receivedData.sequence_id);
    }
    
    markScreenDirtyForFloatData();
    
    lastUpdate = millis();
    
    // Clear calibration mode flag when receiving normal data
    calibrationModeActive = false;
    
  } else if (len == sizeof(calib_command_t)) {
    // Handle calibration command from float unit (trigger)
    onCalibrationCommandFromFloat(mac, incomingData, len);
    
    // Set calibration mode flag when receiving calibration commands
    calibrationModeActive = true;
  } else if (len == sizeof(calib_response_t)) {
    // Handle calibration response from float unit
    onCalibrationResponse(mac, incomingData, len);
    
    // Set calibration mode flag when receiving calibration responses
    calibrationModeActive = true;
  } else {
    LOG_ERROR("Unknown data format received: %d bytes\n", len);
  }
}

void addDataPoint(payload_t data, uint32_t epoch_s) {
  displayDataBuffer[displayDataIndex] = data;
  displayTimestampBuffer[displayDataIndex] = epoch_s;
  displayDataIndex = (displayDataIndex + 1) % MAX_DATA_POINTS;
  
  if (displayDataCount < MAX_DATA_POINTS) {
    displayDataCount++;
  }
  
  if (dischargeRateBufferCount < 25) {
    dischargeRateBuffer[dischargeRateBufferCount] = data;
    dischargeRateTimestampBuffer[dischargeRateBufferCount] = epoch_s;
    dischargeRateBufferCount++;
  } else {
    for (int i = 1; i < 25; i++) {
      dischargeRateBuffer[i - 1] = dischargeRateBuffer[i];
      dischargeRateTimestampBuffer[i - 1] = dischargeRateTimestampBuffer[i];
    }
    dischargeRateBuffer[24] = data;
    dischargeRateTimestampBuffer[24] = epoch_s;
  }
}

void clearHistoricalDisplayData() {
  displayDataIndex = 0;
  displayDataCount = 0;
  totalCSVDataLines = 0;
  lastHistoricalLoadedLines = 0;
  lastHistoricalSkippedLines = 0;
  lastHistoricalParseErrors = 0;
  lastHistoricalPreBatchLines = 0;
  lastHistoricalPostBatchLines = 0;
  lastHistoricalBatchFilteredLines = 0;
  lastHistoricalCutoffFilteredLines = 0;
  lastHistoricalBatchStartRelaxed = false;
  lastHistoricalOldestEpoch = 0;
  lastHistoricalNewestEpoch = 0;
  oldestBufferedMillis = 0;
  dischargeRateBufferCount = 0;
  memset(displayDataBuffer, 0, sizeof(displayDataBuffer));
  memset(displayTimestampBuffer, 0, sizeof(displayTimestampBuffer));
  memset(dischargeRateBuffer, 0, sizeof(dischargeRateBuffer));
  memset(dischargeRateTimestampBuffer, 0, sizeof(dischargeRateTimestampBuffer));
  previousAnalyticsSG = 0.0f;
  previousAnalyticsEpoch = 0;
}

void clearBufferedSensorData() {
  bufferIndex = 0;
  bufferedCount = 0;
  oldestBufferedMillis = 0;
  memset(dataBuffer, 0, sizeof(dataBuffer));
}

bool shouldRecordBatchFloatData() {
  if (!brewProfileLoaded) return fermentationFileOpen && currentFermentationFile[0] != '\0';
  if (activeBrewProfile.completed) return false;
  if (isPostPackageTemperaturePhase()) return false;
  return activeBrewProfile.floatInBrewConfirmed || activeBrewProfile.ogVerified;
}

void finalizeHistoricalDataLoad() {
  if (displayDataCount > 0) {
    cursorPosition = 1.0f;
    cursorIndex = displayDataCount - 1;
    refreshFermentationAssistantFromProfile();
    lastUpdate = millis();
  }

  staticElementsDrawn = false;
  heroDirty = true;
  tileTempDirty = true;
  tileAngleDirty = true;
  tileAbvDirty = true;
  topbarDirty = true;
  detailsDirty = true;
  screenDirty = true;
}

void markScreenDirtyForFloatData() {
  static bool lastHadData = false;
  bool hasData = displayDataCount > 0;

  heroDirty = true;
  tileTempDirty = true;
  tileAngleDirty = true;
  tileAbvDirty = true;
  topbarDirty = true;
  detailsDirty = true;

  if (!lastHadData && hasData) {
    staticElementsDrawn = false;
  }
  lastHadData = hasData;

  screenDirty = true;
}

int displayBufferIndexForPoint(int pointIndex) {
  return (displayDataIndex - displayDataCount + pointIndex + MAX_DATA_POINTS) % MAX_DATA_POINTS;
}

uint32_t timestampForPoint(int pointIndex) {
  if (pointIndex < 0 || pointIndex >= displayDataCount) {
    return 0;
  }
  return displayTimestampBuffer[displayBufferIndexForPoint(pointIndex)];
}

bool timestampsAvailableForGraph() {
  if (displayDataCount < 2) return false;
  uint32_t firstEpoch = timestampForPoint(0);
  uint32_t lastEpoch = timestampForPoint(displayDataCount - 1);
  return isEpochValid(firstEpoch) && isEpochValid(lastEpoch) && lastEpoch > firstEpoch;
}

int graphXForPoint(int pointIndex, int graphX, int graphW) {
  if (displayDataCount < 2) return graphX;
  
  if (timestampsAvailableForGraph()) {
    uint32_t firstEpoch = timestampForPoint(0);
    uint32_t lastEpoch = timestampForPoint(displayDataCount - 1);
    uint32_t pointEpoch = timestampForPoint(pointIndex);
    if (isEpochValid(pointEpoch)) {
      return graphX + (int)(((double)(pointEpoch - firstEpoch) * graphW) / (double)(lastEpoch - firstEpoch));
    }
  }
  
  return graphX + (pointIndex * graphW / (displayDataCount - 1));
}

bool calculateTimestampTrend(float latestDensity, uint32_t latestEpoch, float* trendOut) {
  if (!isEpochValid(latestEpoch) || displayDataCount < 2) return false;
  
  const uint32_t TREND_WINDOW_S = 5 * 60;
  for (int i = displayDataCount - 2; i >= 0; i--) {
    uint32_t pointEpoch = timestampForPoint(i);
    if (isEpochValid(pointEpoch) && latestEpoch >= pointEpoch &&
        latestEpoch - pointEpoch >= TREND_WINDOW_S) {
      int idx = displayBufferIndexForPoint(i);
      *trendOut = latestDensity - displayDataBuffer[idx].density;
      return true;
    }
  }
  
  return false;
}

void drawLiveViewStatic() {
  // Draw top bar
  drawViewTopbar("Live");
  
  // Draw calibration warning if active (compact)
  if (calibrationModeActive) {
    // Clear the area first to prevent artefacts
    tft.fillRect(MARGIN - 2, TOPBAR_H + 2, UI_W - MARGIN * 2 + 4, 20, uiColorBackground);
    tft.setTextColor(uiColorError);
    tft.setFreeFont(FONT_SIZE_SM);
    tft.setCursor(MARGIN, TOPBAR_H + 6);  // Adjust for FreeFont baseline
    tft.print("CALIB MODE");
  }
  
  int contentY = calibrationModeActive ? TOPBAR_H + MARGIN + 14 : TOPBAR_H + MARGIN;
  int contentH = UI_H - contentY - NAV_H;
  bool floatOff = isFloatInactiveAfterPackaging();
  
  // No data state
  if (displayDataCount == 0 && !floatOff) {
    int cardX = UI_W / 2 - 100;
    int cardY = contentY + contentH / 2 - 40;
    uiCard(cardX, cardY, 200, 80, CARD_RADIUS);
    
    // Centered error message
    uiTextCenter(cardX, cardY + 20, 200, 20, "No Data received", FONT_SIZE_SM, uiColorTextMuted);
    uiTextCenter(cardX, cardY + 45, 200, 20, "Waiting...", FONT_SIZE_SM, uiColorTextMuted);
    
    uiDrawBottomNav(TAB_LIVE);
    return;
  }
  
  // Hero card (full width)
  payload_t latest = {0};
  if (displayDataCount > 0) {
    latest = displayDataBuffer[(displayDataIndex - 1 + MAX_DATA_POINTS) % MAX_DATA_POINTS];
  }
  int heroH = contentH / 2;
  uiCard(MARGIN, contentY, UI_W - MARGIN * 2, heroH, CARD_RADIUS);
  
  if (floatOff) {
    uiTextCenter(MARGIN, contentY + 0, UI_W - MARGIN * 2, 26,
                 "Packaged", FONT_SIZE_MD, uiColorInfo);
    char finalLine[32];
    if (brewProfileLoaded) snprintf(finalLine, sizeof(finalLine), "Final SG %.3f", activeBrewProfile.expectedFinalGravity);
    else strncpy(finalLine, "Float off", sizeof(finalLine) - 1);
    finalLine[sizeof(finalLine) - 1] = '\0';
    uiTextCenter(MARGIN, contentY + 34, UI_W - MARGIN * 2, 22,
                 finalLine, FONT_SIZE_SM, uiColorTextSecondary);
  } else {
    // Prepare sparkline data (last ~20 SG readings)
    float sparklineData[20];
    int sparklineCount = 0;
    int pointsToShow = min(displayDataCount, 20);
    for (int i = 0; i < pointsToShow; i++) {
      int idx = (displayDataIndex - pointsToShow + i + MAX_DATA_POINTS) % MAX_DATA_POINTS;
      sparklineData[i] = displayDataBuffer[idx].density;
      sparklineCount++;
    }

    uiHeroSG(MARGIN, contentY, UI_W - MARGIN * 2, heroH, latest.density, "", sparklineData, sparklineCount);
  }
  
  // 3 tiles below hero (Temp, Angle, ABV) - Batt moved to LIVE_DETAILS_VIEW
  int tileY = contentY + heroH + GAP - 6;  // Lifted by 6px
  int tileW = (UI_W - MARGIN * 2 - GAP * 2) / 3;  // 3 tiles with gaps
  int tileH = contentH - heroH - GAP;
  
  uiTile(MARGIN, tileY, tileW, tileH, 0, "Temp", "--", "C", false);
  if (floatOff) drawFloatOffAngleTile(MARGIN + tileW + GAP, tileY, tileW, tileH);
  else uiTile(MARGIN + tileW + GAP, tileY, tileW, tileH, 0, "Angle", "--", "deg", false);
  uiTile(MARGIN + tileW * 2 + GAP * 2, tileY, tileW, tileH, 0, "ABV", floatOff ? "Final" : "Set OG", "%", true);
  
  // Bottom navigation
  uiDrawBottomNav(TAB_LIVE);
  
  // Reset dirty flags
  heroDirty = true;
  tileTempDirty = true;
  tileAngleDirty = true;
  tileAbvDirty = true;
  staticElementsDrawn = false;  // Force full redraw after tile position change
}

void updateLiveViewDynamic() {
  bool floatOff = isFloatInactiveAfterPackaging();
  if (displayDataCount == 0 && !floatOff) {
    return;
  }
  
  // Get latest data
  payload_t latest = {0};
  if (displayDataCount > 0) {
    latest = displayDataBuffer[(displayDataIndex - 1 + MAX_DATA_POINTS) % MAX_DATA_POINTS];
  }
  uint8_t batteryPercent = calculateBatteryPercentage(latest.battery_voltage);
  
  int contentY = calibrationModeActive ? TOPBAR_H + MARGIN + 14 : TOPBAR_H + MARGIN;
  int contentH = UI_H - contentY - NAV_H;
  int heroH = contentH / 2;
  int tileY = contentY + heroH + GAP - 6;  // Lifted by 6px
  int tileW = (UI_W - MARGIN * 2 - GAP * 2) / 3;  // 3 tiles
  int tileH = contentH - heroH - GAP;
  
  char buffer[16];
  
  // Update hero SG value with trend and sparkline
  if (heroDirty) {
    if (floatOff) {
      uiCard(MARGIN, contentY, UI_W - MARGIN * 2, heroH, CARD_RADIUS);
      uiTextCenter(MARGIN, contentY + 0, UI_W - MARGIN * 2, 26,
                   "Packaged", FONT_SIZE_MD, uiColorInfo);
      char finalLine[32];
      if (brewProfileLoaded) snprintf(finalLine, sizeof(finalLine), "Final SG %.3f", activeBrewProfile.expectedFinalGravity);
      else strncpy(finalLine, "Float off", sizeof(finalLine) - 1);
      finalLine[sizeof(finalLine) - 1] = '\0';
      uiTextCenter(MARGIN, contentY + 34, UI_W - MARGIN * 2, 22,
                   finalLine, FONT_SIZE_SM, uiColorTextSecondary);
      heroDirty = false;
    } else {
    // Calculate trend against the reading closest to at least 5 real minutes ago.
    char trendBuf[16] = "";
    float trend = 0.0;
    uint32_t latestEpoch = displayTimestampBuffer[(displayDataIndex - 1 + MAX_DATA_POINTS) % MAX_DATA_POINTS];
    bool hasTrend = calculateTimestampTrend(latest.density, latestEpoch, &trend);
    if (!hasTrend && displayDataCount >= 10) {
      int oldIdx = (displayDataIndex - 10 + MAX_DATA_POINTS) % MAX_DATA_POINTS;
        trend = latest.density - displayDataBuffer[oldIdx].density;
      hasTrend = true;
    }
    if (hasTrend) {
      if (abs(trend) >= 0.001) {
        snprintf(trendBuf, sizeof(trendBuf), "%+.3f", trend);
      }
    }
    
    // Prepare sparkline data (last ~20 SG readings)
    float sparklineData[20];
    int sparklineCount = 0;
    int pointsToShow = min(displayDataCount, 20);
    for (int i = 0; i < pointsToShow; i++) {
      int idx = (displayDataIndex - pointsToShow + i + MAX_DATA_POINTS) % MAX_DATA_POINTS;
      sparklineData[i] = displayDataBuffer[idx].density;
      sparklineCount++;
    }
    
    uiHeroSG(MARGIN, contentY, UI_W - MARGIN * 2, heroH, latest.density, 
             trendBuf[0] ? trendBuf : "", sparklineData, sparklineCount);
    heroDirty = false;
    }
  }
  
  // Update temp tile
  if (tileTempDirty) {
    snprintf(buffer, sizeof(buffer), "%.1f", latestDisplayedTemperatureC());
    uiTile(MARGIN, tileY, tileW, tileH, 0, "Temp", buffer, "C", false);
    tileTempDirty = false;
  }
  
  // Update angle tile
  if (tileAngleDirty) {
    if (floatOff) {
      drawFloatOffAngleTile(MARGIN + tileW + GAP, tileY, tileW, tileH);
    } else {
      snprintf(buffer, sizeof(buffer), "%.1f", latest.angle);
      uiTile(MARGIN + tileW + GAP, tileY, tileW, tileH, 0, "Angle", buffer, "deg", false);
    }
    tileAngleDirty = false;
  }
  
  // Update ABV tile
  if (tileAbvDirty) {
    if (ogCaptured) {
      snprintf(buffer, sizeof(buffer), "%.1f", currentABV);
      uiTile(MARGIN + tileW * 2 + GAP * 2, tileY, tileW, tileH, 0,
             floatOff ? "Final ABV" : "ABV", buffer, "%", false);
    } else {
      uiTile(MARGIN + tileW * 2 + GAP * 2, tileY, tileW, tileH, 0, "ABV", "Set OG", "%", true);
    }
    tileAbvDirty = false;
  }
}

void drawFloatOffAngleTile(int x, int y, int w, int h) {
  uiCard(x, y, w, h, CARD_RADIUS);
  tft.setTextColor(uiColorTextMuted);
  tft.setFreeFont(FONT_SIZE_SM);
  tft.setCursor(x + 16, y + 25);
  tft.print("Angle");

  const char* value = "Float off";
  tft.setFreeFont(FONT_SIZE_MD);
  int valueW = tft.textWidth(value);
  int valueH = tft.fontHeight();
  int valueX = x + (w - valueW) / 2;
  int valueY = y + h / 2 + valueH / 2 - 2;
  tft.setCursor(valueX, valueY);
  tft.print(value);
}

void drawLiveView() {
  // Check if we're transitioning from no-data to data state
  static bool lastHadData = false;
  bool hasData = displayDataCount > 0;
  
  // Force complete screen clear on data state transitions to prevent artefacts
  if (!staticElementsDrawn || currentMode != LIVE_VIEW || 
      (lastHadData && !hasData) || (!lastHadData && hasData)) {
    tft.fillScreen(uiColorBackground);
    // Also clear any calibration warning area that might remain
    if (!hasData && calibrationModeActive) {
      tft.fillRect(MARGIN - 2, TOPBAR_H + 2, UI_W - MARGIN * 2 + 4, 20, uiColorBackground);
    }
    staticElementsDrawn = false;  // Force full redraw
  }
  
  // Always redraw static elements when needed
  if (!staticElementsDrawn) {
    drawLiveViewStatic();
    staticElementsDrawn = true;
  }
  
  updateLiveViewDynamic();
  
  lastHadData = hasData;
}

void drawGraphView() {
  tft.fillScreen(uiColorBackground);
  
  drawViewTopbar("Graph");
  
  // Define button area
  #define GRAPH_BUTTON_H 40
  #define GRAPH_BUTTON_Y (UI_H - NAV_H - GRAPH_BUTTON_H - GAP)
  
  int contentY = TOPBAR_H + MARGIN;
  int contentH = GRAPH_BUTTON_Y - contentY - GAP;
  
  if (displayDataCount < 3) {
    drawNoDataCard("No graph data", "Collect a few points first", TAB_GRAPH);
    return;
  }
  
  // Initialize cursor to last data point (100%) only if cursor is at invalid position
  if (cursorIndex < 0 || cursorIndex >= displayDataCount) {
    cursorPosition = 1.0;
    cursorIndex = displayDataCount - 1;
  }
  
  // Draw graph card
  uiCard(MARGIN, contentY, UI_W - MARGIN * 2, contentH, CARD_RADIUS);
  drawGraph();
  
  // Draw 5 buttons in a single row below graph
  int buttonW = (UI_W - MARGIN * 2 - GAP * 4) / 5;
  int buttonX = MARGIN;
  
  // 6h button
  drawButton(buttonX, GRAPH_BUTTON_Y, buttonW, GRAPH_BUTTON_H, "6h", currentLoadMode == LOAD_6H);
  buttonX += buttonW + GAP;
  
  // 24h button
  drawButton(buttonX, GRAPH_BUTTON_Y, buttonW, GRAPH_BUTTON_H, "24h", currentLoadMode == LOAD_24H);
  buttonX += buttonW + GAP;
  
  // All button
  drawButton(buttonX, GRAPH_BUTTON_Y, buttonW, GRAPH_BUTTON_H, "All", currentLoadMode == LOAD_ALL);
  buttonX += buttonW + GAP;
  
  // < button
  drawButton(buttonX, GRAPH_BUTTON_Y, buttonW, GRAPH_BUTTON_H, "<", false);
  buttonX += buttonW + GAP;
  
  // > button
  drawButton(buttonX, GRAPH_BUTTON_Y, buttonW, GRAPH_BUTTON_H, ">", false);
  
  uiDrawBottomNav(TAB_GRAPH);
}

void drawRecommendationPanel(int x, int y, int w, int h) {
  uiCard(x, y, w, h, CARD_RADIUS);
  tft.setTextColor(uiColorAccent);
  tft.setFreeFont(FONT_SIZE_SM);
  tft.setCursor(x + 10, y + 22);
  tft.print("Next action");
  tft.setTextColor(uiColorTextPrimary);
  tft.setFreeFont(FONT_SIZE_SM);
  char message[64];
  uiEllipsize(currentRecommendation.message, w - 20, message, sizeof(message));
  tft.setCursor(x + 10, y + 50);
  tft.print(message);
}

void formatActionHeader(char* buffer, size_t bufferSize) {
  if (!buffer || bufferSize == 0) return;
  const char* prefix = currentBatchAction.requiresChoice ? "ACTION REQUIRED" : "NEXT";
  if (!currentBatchAction.requiresChoice && currentBatchAction.secondsUntilDue > 0) {
    char duration[16];
    formatDurationShort(currentBatchAction.secondsUntilDue, duration, sizeof(duration));
    snprintf(buffer, bufferSize, "%s (%s)", prefix, duration);
  } else {
    snprintf(buffer, bufferSize, "%s", prefix);
  }
}

void drawDashboardScreen() {
  tft.fillScreen(uiColorBackground);
  drawViewTopbar("Dashboard");
  topbarDirty = false;
  heroDirty = false;
  tileTempDirty = false;
  tileAngleDirty = false;
  tileAbvDirty = false;

  int contentY = TOPBAR_H + MARGIN;
  int contentW = UI_W - MARGIN * 2;

  if (!brewProfileLoaded) {
    uiCard(MARGIN, contentY + 34, contentW, 112, CARD_RADIUS);
    uiTextCenter(MARGIN, contentY + 56, contentW, 24, "No active batch", FONT_SIZE_MD, uiColorTextPrimary);
    uiTextCenter(MARGIN, contentY + 90, contentW, 24, "More > New Brew", FONT_SIZE_SM, uiColorTextMuted);
    uiDrawBottomNav(TAB_DASHBOARD);
    return;
  }

  payload_t latest = {0};
  bool hasData = displayDataCount > 0;
  if (hasData) {
    latest = displayDataBuffer[(displayDataIndex - 1 + MAX_DATA_POINTS) % MAX_DATA_POINTS];
  }

  const int dashGap = 6;
  const int summaryH = 34;
  const int actionH = 86;
  const int metricH = 52;
  const int contextH = 38;
  char text[64];
  char value[24];

  // Summary strip: batch + phase only
  uiCard(MARGIN, contentY, contentW, summaryH, CARD_RADIUS);
  uiEllipsize(activeBrewProfile.batchName, contentW - 22, text, sizeof(text));
  tft.setTextColor(uiColorTextPrimary);
  tft.setFreeFont(FONT_SIZE_XS);
  tft.setCursor(MARGIN + 10, contentY + 14);
  tft.print(text);
  char phaseText[64];
  snprintf(phaseText, sizeof(phaseText), "%s | %s", activeBrewProfile.beerStyle,
           currentDisplayPhaseName(getCurrentEpoch()));
  uiEllipsize(phaseText, contentW - 22, text, sizeof(text));
  tft.setTextColor(uiColorTextMuted);
  tft.setCursor(MARGIN + 10, contentY + 30);
  tft.print(text);

  // Primary focus: next action panel
  int actionY = contentY + summaryH + dashGap;
  uiCard(MARGIN, actionY, contentW, actionH, CARD_RADIUS);
  char actionHeader[28];
  formatActionHeader(actionHeader, sizeof(actionHeader));
  tft.setTextColor(currentBatchAction.requiresChoice ? uiColorWarning : uiColorTextMuted);
  tft.setFreeFont(FONT_SIZE_XS);
  tft.setCursor(MARGIN + 10, actionY + 13);
  tft.print(actionHeader);
  tft.setTextColor(uiColorTextPrimary);
  tft.setFreeFont(FONT_SIZE_SM);
  uiEllipsize(currentBatchAction.title, contentW - 20, text, sizeof(text));
  tft.setCursor(MARGIN + 10, actionY + 34);
  tft.print(text);
  bool singleActionButton = currentBatchAction.type == ACTION_FLOAT_IN_BREW ||
                            currentBatchAction.type == ACTION_PACKAGE_COMPLETE;
  drawWrappedText(MARGIN + 10, actionY + 50, contentW - (currentBatchAction.requiresChoice ? (singleActionButton ? 106 : 196) : 20),
                  currentBatchAction.type == ACTION_NONE ? currentRecommendation.message : currentBatchAction.message,
                  uiColorTextSecondary);
  if (currentBatchAction.requiresChoice) {
    int buttonW = 86;
    int buttonY = actionY + actionH - 32;
    int skipX = MARGIN + contentW - buttonW * 2 - GAP - 10;
    int doneX = MARGIN + contentW - buttonW - 10;
    if (!singleActionButton) {
      tft.fillRoundRect(skipX, buttonY, buttonW, 28, 8, uiColorCardBackground);
      tft.drawRoundRect(skipX, buttonY, buttonW, 28, 8, uiColorBorder);
      uiTextCenter(skipX, buttonY, buttonW, 28, "SKIP", FONT_SIZE_XS, uiColorTextPrimary);
    }
    tft.fillRoundRect(doneX, buttonY, buttonW, 28, 8, uiColorGold);
    const char* doneLabel = "DONE";
    if (currentBatchAction.type == ACTION_FLOAT_ZERO_CAL) doneLabel = "READY";
    if (currentBatchAction.type == ACTION_PACKAGE_START) doneLabel = "START";
    uiTextCenter(doneX, buttonY, buttonW, 28,
                 doneLabel, FONT_SIZE_XS, uiColorPrimaryText);
  }

  // 4 core metrics in one calm row
  int metricY = actionY + actionH + dashGap;
  int tileW = (contentW - GAP * 3) / 4;
  const char* labels[4] = {"Atten", "ABV", "FG", "ETA"};
  for (int i = 0; i < 4; i++) {
    int x = MARGIN + i * (tileW + GAP);
    uiCard(x, metricY, tileW, metricH, CARD_RADIUS);
    tft.setTextColor(uiColorTextMuted);
    tft.setFreeFont(FONT_SIZE_XS);
    tft.setCursor(x + 10, metricY + 14);
    tft.print(labels[i]);
    tft.setTextColor(uiColorTextPrimary);
    tft.setFreeFont(FONT_SIZE_SM);
    if (i == 0) {
      if (hasData) snprintf(value, sizeof(value), "%.0f%%", fermentationMetrics.currentAttenuation);
      else strcpy(value, "--");
    } else if (i == 1) {
      if (hasData) snprintf(value, sizeof(value), "%.1f%%", fermentationMetrics.estimatedABV);
      else strcpy(value, "--");
    } else if (i == 2) {
      snprintf(value, sizeof(value), "%.3f", activeBrewProfile.expectedFinalGravity);
    } else {
      if (currentETA.valid) formatDurationShort(currentETA.secondsToPackaging, value, sizeof(value));
      else strcpy(value, "--");
    }
    tft.setCursor(x + 10, metricY + 36);
    tft.print(value);
  }

  // Minimal context row (only what helps decisions)
  int contextY = metricY + metricH + dashGap;
  int halfW = (contentW - GAP) / 2;
  uiCard(MARGIN, contextY, halfW, contextH, CARD_RADIUS);
  tft.setTextColor(uiColorTextMuted);
  tft.setFreeFont(FONT_SIZE_XS);
  tft.setCursor(MARGIN + 10, contextY + 14);
  tft.print("OG");
  if (activeBrewProfile.ogNeedsChoice) strcpy(text, "Verify pending");
  else if (activeBrewProfile.ogVerified) snprintf(text, sizeof(text), "OK %.3f", activeBrewProfile.effectiveOG);
  else strcpy(text, "Measuring");
  tft.setTextColor(uiColorTextPrimary);
  tft.setCursor(MARGIN + 10, contextY + 30);
  tft.print(text);

  int tempX = MARGIN + halfW + GAP;
  uiCard(tempX, contextY, halfW, contextH, CARD_RADIUS);
  tft.setTextColor(uiColorTextMuted);
  tft.setFreeFont(FONT_SIZE_XS);
  tft.setCursor(tempX + 10, contextY + 14);
  tft.print("Temp");
  float tempTarget = currentTemperatureTargetC(getCurrentEpoch());
  float displayTempC = latestDisplayedTemperatureC();
  bool hasDisplayTemp = !isnan(displayTempC) && !isinf(displayTempC);
  if (currentBatchAction.type == ACTION_PACKAGE_START &&
      activeBrewProfile.temperatureProfile.enabled &&
      !activeBrewProfile.packageDone &&
      !activeBrewProfile.packageSkipped) {
    float nextTarget = activeBrewProfile.temperatureProfile.advanced.carbonationC;
    if (hasDisplayTemp) snprintf(text, sizeof(text), "%.1f C | Pack %.1f C", displayTempC, nextTarget);
    else snprintf(text, sizeof(text), "-- | Pack %.1f C", nextTarget);
  } else if (hasDisplayTemp) {
    snprintf(text, sizeof(text), "%.1f C | Set %.1f C", displayTempC, tempTarget);
  } else {
    snprintf(text, sizeof(text), "-- | Set %.1f C", tempTarget);
  }
  tft.setTextColor(uiColorTextPrimary);
  tft.setCursor(tempX + 10, contextY + 30);
  tft.print(text);
  uiDrawBottomNav(TAB_DASHBOARD);
}

static const char* YEAST_SPEED_OPTIONS[] = {"slow", "medium", "medium-fast", "fast", "very_fast"};
static const char* YEAST_FLOC_OPTIONS[] = {"low", "medium", "high"};
static const char* YEAST_CURVE_OPTIONS[] = {"clean_ale", "fast_ale", "very_fast_ale", "slow_clean_ale", "lager", "high_attenuation_saison"};

void copyPresetToDraft(const YeastPreset* preset) {
  memset(&yeastDraft, 0, sizeof(yeastDraft));
  if (!preset) {
    strcpy(yeastDraft.id, "");
    strcpy(yeastDraft.displayName, "New Yeast");
    strcpy(yeastDraft.category, "Custom");
    yeastDraft.typicalAttenuationMin = 74;
    yeastDraft.typicalAttenuationMax = 80;
    yeastDraft.defaultAttenuation = 77;
    strcpy(yeastDraft.fermentationSpeed, "medium");
    yeastDraft.lagPhaseHours = 9.0f;
    yeastDraft.typicalDurationHours = 132.0f;
    yeastDraft.recommendedTempMinC = 18.0f;
    yeastDraft.recommendedTempMaxC = 22.0f;
    strcpy(yeastDraft.flocculation, "medium");
    strcpy(yeastDraft.curveTemplate, "clean_ale");
    yeastDraft.diacetylRestRecommended = false;
    strcpy(yeastDraft.notes, "Custom yeast");
    return;
  }
  strncpy(yeastDraft.id, preset->id, sizeof(yeastDraft.id) - 1);
  strncpy(yeastDraft.displayName, preset->displayName, sizeof(yeastDraft.displayName) - 1);
  strncpy(yeastDraft.category, preset->category, sizeof(yeastDraft.category) - 1);
  yeastDraft.typicalAttenuationMin = preset->typicalAttenuationMin;
  yeastDraft.typicalAttenuationMax = preset->typicalAttenuationMax;
  yeastDraft.defaultAttenuation = preset->defaultAttenuation;
  strncpy(yeastDraft.fermentationSpeed, preset->fermentationSpeed, sizeof(yeastDraft.fermentationSpeed) - 1);
  yeastDraft.lagPhaseHours = preset->lagPhaseHours;
  yeastDraft.typicalDurationHours = preset->typicalDurationHours;
  yeastDraft.recommendedTempMinC = preset->recommendedTempMinC;
  yeastDraft.recommendedTempMaxC = preset->recommendedTempMaxC;
  strncpy(yeastDraft.flocculation, preset->flocculation, sizeof(yeastDraft.flocculation) - 1);
  strncpy(yeastDraft.curveTemplate, preset->curveTemplate, sizeof(yeastDraft.curveTemplate) - 1);
  yeastDraft.diacetylRestRecommended = preset->diacetylRestRecommended;
  strncpy(yeastDraft.notes, preset->notes, sizeof(yeastDraft.notes) - 1);
}

int optionIndex(const char* value, const char* const* options, int count) {
  for (int i = 0; i < count; i++) {
    if (strcmp(value, options[i]) == 0) return i;
  }
  return 0;
}

void selectOptionOffset(char* target, size_t targetSize, const char* const* options, int count, int offset) {
  int idx = optionIndex(target, options, count) + offset;
  if (idx < 0) idx = count - 1;
  if (idx >= count) idx = 0;
  strncpy(target, options[idx], targetSize - 1);
  target[targetSize - 1] = '\0';
}

void beginNewYeastWizard(const char* presetId) {
  if (mountSDTemporarily()) {
    YeastPresetRepository::reloadCustom();
    const YeastPreset* preset = presetId ? YeastPresetRepository::findById(presetId) : NULL;
    editingExistingYeast = presetId && YeastPresetRepository::isCustom(presetId);
    copyPresetToDraft(editingExistingYeast ? preset : NULL);
    dismountSD();
  } else {
    editingExistingYeast = false;
    copyPresetToDraft(NULL);
  }
  newYeastStep = NY_NAME;
  loadYeastStepBuffer();
  currentMode = NEW_YEAST_VIEW;
  screenDirty = true;
}

void loadYeastStepBuffer() {
  yeastEditPristine = false;
  switch (newYeastStep) {
    case NY_NAME:
      strncpy(yeastEditBuffer, yeastDraft.displayName, sizeof(yeastEditBuffer) - 1);
      yeastEditPristine = true;
      break;
    case NY_CATEGORY:
      strncpy(yeastEditBuffer, yeastDraft.category, sizeof(yeastEditBuffer) - 1);
      yeastEditPristine = true;
      break;
    case NY_ATT_MIN:
      snprintf(yeastEditBuffer, sizeof(yeastEditBuffer), "%d", yeastDraft.typicalAttenuationMin);
      yeastEditPristine = true;
      break;
    case NY_ATT_MAX:
      snprintf(yeastEditBuffer, sizeof(yeastEditBuffer), "%d", yeastDraft.typicalAttenuationMax);
      yeastEditPristine = true;
      break;
    case NY_ATT_DEFAULT:
      snprintf(yeastEditBuffer, sizeof(yeastEditBuffer), "%d", yeastDraft.defaultAttenuation);
      yeastEditPristine = true;
      break;
    case NY_LAG:
      snprintf(yeastEditBuffer, sizeof(yeastEditBuffer), "%.1f", yeastDraft.lagPhaseHours);
      yeastEditPristine = true;
      break;
    case NY_DURATION:
      snprintf(yeastEditBuffer, sizeof(yeastEditBuffer), "%.1f", yeastDraft.typicalDurationHours);
      yeastEditPristine = true;
      break;
    case NY_TEMP_MIN:
      snprintf(yeastEditBuffer, sizeof(yeastEditBuffer), "%.1f", yeastDraft.recommendedTempMinC);
      yeastEditPristine = true;
      break;
    case NY_TEMP_MAX:
      snprintf(yeastEditBuffer, sizeof(yeastEditBuffer), "%.1f", yeastDraft.recommendedTempMaxC);
      yeastEditPristine = true;
      break;
    case NY_NOTES:
      strncpy(yeastEditBuffer, yeastDraft.notes, sizeof(yeastEditBuffer) - 1);
      yeastEditPristine = true;
      break;
    default:
      yeastEditBuffer[0] = '\0';
      break;
  }
  yeastEditBuffer[sizeof(yeastEditBuffer) - 1] = '\0';
}

void commitYeastStepBuffer() {
  switch (newYeastStep) {
    case NY_NAME:
      if (yeastEditBuffer[0]) strncpy(yeastDraft.displayName, yeastEditBuffer, sizeof(yeastDraft.displayName) - 1);
      break;
    case NY_CATEGORY:
      if (yeastEditBuffer[0]) strncpy(yeastDraft.category, yeastEditBuffer, sizeof(yeastDraft.category) - 1);
      break;
    case NY_ATT_MIN:
      yeastDraft.typicalAttenuationMin = atoi(yeastEditBuffer);
      break;
    case NY_ATT_MAX:
      yeastDraft.typicalAttenuationMax = atoi(yeastEditBuffer);
      break;
    case NY_ATT_DEFAULT:
      yeastDraft.defaultAttenuation = atoi(yeastEditBuffer);
      break;
    case NY_LAG:
      yeastDraft.lagPhaseHours = atof(yeastEditBuffer);
      break;
    case NY_DURATION:
      yeastDraft.typicalDurationHours = atof(yeastEditBuffer);
      break;
    case NY_TEMP_MIN:
      yeastDraft.recommendedTempMinC = atof(yeastEditBuffer);
      break;
    case NY_TEMP_MAX:
      yeastDraft.recommendedTempMaxC = atof(yeastEditBuffer);
      break;
    case NY_NOTES:
      if (yeastEditBuffer[0]) strncpy(yeastDraft.notes, yeastEditBuffer, sizeof(yeastDraft.notes) - 1);
      break;
    default:
      break;
  }
  yeastDraft.displayName[sizeof(yeastDraft.displayName) - 1] = '\0';
  yeastDraft.category[sizeof(yeastDraft.category) - 1] = '\0';
  yeastDraft.notes[sizeof(yeastDraft.notes) - 1] = '\0';
  if (yeastDraft.typicalAttenuationMin < 40) yeastDraft.typicalAttenuationMin = 40;
  if (yeastDraft.typicalAttenuationMax < yeastDraft.typicalAttenuationMin) yeastDraft.typicalAttenuationMax = yeastDraft.typicalAttenuationMin;
  if (yeastDraft.defaultAttenuation < yeastDraft.typicalAttenuationMin) yeastDraft.defaultAttenuation = yeastDraft.typicalAttenuationMin;
  if (yeastDraft.defaultAttenuation > yeastDraft.typicalAttenuationMax) yeastDraft.defaultAttenuation = yeastDraft.typicalAttenuationMax;
}

void drawNewYeastNav(const char* nextLabel) {
  drawButton(MARGIN, 276, 120, 36, "BACK", false);
  drawButton(UI_W - MARGIN - 140, 276, 140, 36, nextLabel, true);
}

void drawYeastDropdown(const char* label, const char* value) {
  tft.setTextColor(uiColorTextSecondary);
  tft.setFreeFont(FONT_SIZE_SM);
  tft.setCursor(MARGIN, 102);
  tft.print(label);
  drawButton(MARGIN, 126, 58, 54, "<", false);
  uiCard(MARGIN + 68, 126, UI_W - MARGIN * 2 - 136, 54, CARD_RADIUS);
  uiTextCenter(MARGIN + 68, 126, UI_W - MARGIN * 2 - 136, 54, value, FONT_SIZE_SM_BOLD, uiColorTextPrimary);
  drawButton(UI_W - MARGIN - 58, 126, 58, 54, ">", false);
}

void drawNewYeastScreen() {
  tft.fillScreen(uiColorBackground);
  drawViewTopbar(editingExistingYeast ? "Edit Yeast" : "New Yeast");
  char stepText[20];
  snprintf(stepText, sizeof(stepText), "%d/15", (int)newYeastStep + 1);
  uiTextRight(UI_W - 80, TOPBAR_H + 8, 66, 18, stepText, FONT_SIZE_XS, uiColorTextMuted);
  const char* title = "";
  switch (newYeastStep) {
    case NY_NAME: title = "Display Name"; break;
    case NY_CATEGORY: title = "Category"; break;
    case NY_ATT_MIN: title = "Attenuation Min"; break;
    case NY_ATT_MAX: title = "Attenuation Max"; break;
    case NY_ATT_DEFAULT: title = "Default Attenuation"; break;
    case NY_SPEED: title = "Fermentation Speed"; break;
    case NY_LAG: title = "Lag Phase Hours"; break;
    case NY_DURATION: title = "Duration Hours"; break;
    case NY_TEMP_MIN: title = "Temp Min C"; break;
    case NY_TEMP_MAX: title = "Temp Max C"; break;
    case NY_FLOC: title = "Flocculation"; break;
    case NY_CURVE: title = "Curve Template"; break;
    case NY_DREST: title = "Diacetyl Rest"; break;
    case NY_NOTES: title = "Notes"; break;
    case NY_REVIEW: title = "Review Yeast"; break;
  }
  tft.setTextColor(uiColorTextPrimary);
  tft.setFreeFont(FONT_SIZE_SM);
  tft.setCursor(MARGIN, TOPBAR_H + 28);
  tft.print(title);

  if (newYeastStep == NY_NAME || newYeastStep == NY_CATEGORY || newYeastStep == NY_NOTES) {
    VirtualKeyboardInput::drawText(tft, yeastEditBuffer);
  } else if (newYeastStep == NY_ATT_MIN || newYeastStep == NY_ATT_MAX || newYeastStep == NY_ATT_DEFAULT ||
             newYeastStep == NY_LAG || newYeastStep == NY_DURATION || newYeastStep == NY_TEMP_MIN || newYeastStep == NY_TEMP_MAX) {
    VirtualKeyboardInput::drawNumber(tft, yeastEditBuffer);
  } else if (newYeastStep == NY_SPEED) {
    drawYeastDropdown("Speed", yeastDraft.fermentationSpeed);
  } else if (newYeastStep == NY_FLOC) {
    drawYeastDropdown("Flocculation", yeastDraft.flocculation);
  } else if (newYeastStep == NY_CURVE) {
    drawYeastDropdown("Curve", yeastDraft.curveTemplate);
  } else if (newYeastStep == NY_DREST) {
    tft.setTextColor(uiColorTextSecondary);
    tft.setFreeFont(FONT_SIZE_SM);
    tft.setCursor(MARGIN, 130);
    tft.print("Usually benefits from rest");
    drawThemeToggle(UI_W - MARGIN - 70, 110, yeastDraft.diacetylRestRecommended);
  } else if (newYeastStep == NY_REVIEW) {
    uiCard(MARGIN, 82, UI_W - MARGIN * 2, 172, CARD_RADIUS);
    tft.setTextColor(uiColorTextPrimary);
    tft.setFreeFont(FONT_SIZE_SM_BOLD);
    tft.setCursor(MARGIN + 12, 108);
    tft.print(yeastDraft.displayName);
    tft.setTextColor(uiColorTextSecondary);
    tft.setFreeFont(FONT_SIZE_XS);
    tft.setCursor(MARGIN + 12, 134);
    tft.printf("%s  %d-%d%% default %d%%", yeastDraft.category, yeastDraft.typicalAttenuationMin, yeastDraft.typicalAttenuationMax, yeastDraft.defaultAttenuation);
    tft.setCursor(MARGIN + 12, 158);
    tft.printf("%s  lag %.1fh  duration %.0fh", yeastDraft.fermentationSpeed, yeastDraft.lagPhaseHours, yeastDraft.typicalDurationHours);
    tft.setCursor(MARGIN + 12, 182);
    tft.printf("Temp %.0f-%.0fC  floc %s", yeastDraft.recommendedTempMinC, yeastDraft.recommendedTempMaxC, yeastDraft.flocculation);
    tft.setCursor(MARGIN + 12, 206);
    tft.printf("%s  D-rest %s", yeastDraft.curveTemplate, yeastDraft.diacetylRestRecommended ? "yes" : "no");
    char note[48];
    uiEllipsize(yeastDraft.notes, UI_W - MARGIN * 2 - 24, note, sizeof(note));
    tft.setCursor(MARGIN + 12, 230);
    tft.print(note);
  }
  drawNewYeastNav(newYeastStep == NY_REVIEW ? "SAVE" : "NEXT");
}

void saveNewYeastWizard() {
  YeastPreset preset = {
    yeastDraft.id, yeastDraft.displayName, yeastDraft.category,
    yeastDraft.typicalAttenuationMin, yeastDraft.typicalAttenuationMax, yeastDraft.defaultAttenuation,
    yeastDraft.fermentationSpeed, yeastDraft.lagPhaseHours, yeastDraft.typicalDurationHours,
    yeastDraft.recommendedTempMinC, yeastDraft.recommendedTempMaxC,
    yeastDraft.flocculation, yeastDraft.curveTemplate, yeastDraft.diacetylRestRecommended, yeastDraft.notes
  };
  if (mountSDTemporarily()) {
    YeastPresetRepository::saveCustom(preset);
    YeastPresetRepository::reloadCustom();
    dismountSD();
  }
  loadManagedYeasts();
  currentMode = MANAGE_YEAST_VIEW;
  screenDirty = true;
}

bool handleNewYeastTouch(int x, int y) {
  if (x >= MARGIN - 6 && x <= MARGIN + 130 && y >= 268 && y <= 318) {
    if (newYeastStep == NY_NAME) {
      currentMode = MORE_VIEW;
    } else {
      commitYeastStepBuffer();
      newYeastStep = (NewYeastStep)((int)newYeastStep - 1);
      loadYeastStepBuffer();
    }
    screenDirty = true;
    return true;
  }
  if (x >= UI_W - MARGIN - 146 && x <= UI_W - MARGIN && y >= 268 && y <= 318) {
    commitYeastStepBuffer();
    if (newYeastStep == NY_REVIEW) {
      saveNewYeastWizard();
    } else {
      newYeastStep = (NewYeastStep)((int)newYeastStep + 1);
      loadYeastStepBuffer();
      screenDirty = true;
    }
    return true;
  }
  if (newYeastStep == NY_NAME || newYeastStep == NY_CATEGORY || newYeastStep == NY_NOTES) {
    if (VirtualKeyboardInput::handleTextTouch(x, y, yeastEditBuffer, sizeof(yeastEditBuffer), &yeastEditPristine)) {
      screenDirty = true;
      return true;
    }
  } else if (newYeastStep == NY_ATT_MIN || newYeastStep == NY_ATT_MAX || newYeastStep == NY_ATT_DEFAULT ||
             newYeastStep == NY_LAG || newYeastStep == NY_DURATION || newYeastStep == NY_TEMP_MIN || newYeastStep == NY_TEMP_MAX) {
    if (VirtualKeyboardInput::handleNumberTouch(x, y, yeastEditBuffer, sizeof(yeastEditBuffer), &yeastEditPristine)) {
      screenDirty = true;
      return true;
    }
  } else if (newYeastStep == NY_SPEED || newYeastStep == NY_FLOC || newYeastStep == NY_CURVE) {
    int offset = 0;
    if (x >= MARGIN && x <= MARGIN + 58 && y >= 126 && y <= 180) offset = -1;
    if (x >= UI_W - MARGIN - 58 && x <= UI_W - MARGIN && y >= 126 && y <= 180) offset = 1;
    if (offset != 0) {
      if (newYeastStep == NY_SPEED) selectOptionOffset(yeastDraft.fermentationSpeed, sizeof(yeastDraft.fermentationSpeed), YEAST_SPEED_OPTIONS, 5, offset);
      else if (newYeastStep == NY_FLOC) selectOptionOffset(yeastDraft.flocculation, sizeof(yeastDraft.flocculation), YEAST_FLOC_OPTIONS, 3, offset);
      else selectOptionOffset(yeastDraft.curveTemplate, sizeof(yeastDraft.curveTemplate), YEAST_CURVE_OPTIONS, 6, offset);
      screenDirty = true;
      return true;
    }
  } else if (newYeastStep == NY_DREST) {
    if (x >= UI_W - MARGIN - 86 && x <= UI_W - MARGIN && y >= 100 && y <= 150) {
      yeastDraft.diacetylRestRecommended = !yeastDraft.diacetylRestRecommended;
      screenDirty = true;
      return true;
    }
  }
  return false;
}

void loadManagedYeasts() {
  managedYeastCount = 0;
  if (mountSDTemporarily()) {
    YeastPresetRepository::reloadCustom();
    for (int i = 0; i < YeastPresetRepository::count() && managedYeastCount < 12; i++) {
      const YeastPreset* preset = YeastPresetRepository::at(i);
      if (YeastPresetRepository::isCustom(preset->id)) {
        strncpy(managedYeastIds[managedYeastCount], preset->id, 23);
        managedYeastIds[managedYeastCount][23] = '\0';
        strncpy(managedYeastNames[managedYeastCount], preset->displayName, 31);
        managedYeastNames[managedYeastCount][31] = '\0';
        managedYeastCount++;
      }
    }
    dismountSD();
  }
  if (manageYeastIndex >= managedYeastCount) manageYeastIndex = max(0, managedYeastCount - 1);
}

void drawManageYeastScreen() {
  tft.fillScreen(uiColorBackground);
  drawViewTopbar("Manage Yeast");
  int y = TOPBAR_H + MARGIN;
  if (managedYeastCount == 0) {
    uiCard(MARGIN, y + 44, UI_W - MARGIN * 2, 110, CARD_RADIUS);
    uiTextCenter(MARGIN, y + 68, UI_W - MARGIN * 2, 24, "No custom yeast", FONT_SIZE_MD, uiColorTextPrimary);
    uiTextCenter(MARGIN, y + 102, UI_W - MARGIN * 2, 20, "Use New Yeast first", FONT_SIZE_SM, uiColorTextMuted);
    drawButton(MARGIN, 276, 120, 36, "BACK", false);
    return;
  }
  const YeastPreset* preset = NULL;
  if (mountSDTemporarily()) {
    YeastPresetRepository::reloadCustom();
    preset = YeastPresetRepository::findById(managedYeastIds[manageYeastIndex]);
    dismountSD();
  }
  if (!preset) return;
  uiCard(MARGIN, y, UI_W - MARGIN * 2, 156, CARD_RADIUS);
  tft.setTextColor(uiColorTextPrimary);
  tft.setFreeFont(FONT_SIZE_SM);
  tft.setCursor(MARGIN + 12, y + 28);
  tft.print(preset->displayName);
  tft.setTextColor(uiColorTextSecondary);
  tft.setFreeFont(FONT_SIZE_XS);
  tft.setCursor(MARGIN + 12, y + 54);
  tft.printf("%s  %d-%d%% default %d%%", preset->category, preset->typicalAttenuationMin, preset->typicalAttenuationMax, preset->defaultAttenuation);
  tft.setCursor(MARGIN + 12, y + 78);
  tft.printf("%s  %.0f-%.0fC  %.0fh", preset->fermentationSpeed, preset->recommendedTempMinC, preset->recommendedTempMaxC, preset->typicalDurationHours);
  tft.setCursor(MARGIN + 12, y + 102);
  tft.printf("%s  %s  D-rest %s", preset->curveTemplate, preset->flocculation, preset->diacetylRestRecommended ? "yes" : "no");
  char countText[20];
  snprintf(countText, sizeof(countText), "%d/%d", manageYeastIndex + 1, managedYeastCount);
  uiTextRight(MARGIN, y + 122, UI_W - MARGIN * 2 - 12, 20, countText, FONT_SIZE_XS, uiColorTextMuted);
  drawButton(MARGIN, 214, 72, 36, "<", false);
  drawButton(MARGIN + 84, 214, 110, 36, "EDIT", false);
  drawButton(MARGIN + 206, 214, 110, 36, "DELETE", false);
  drawButton(UI_W - MARGIN - 72, 214, 72, 36, ">", false);
  drawButton(MARGIN, 276, 120, 36, "BACK", false);
}

bool handleManageYeastTouch(int x, int y) {
  if (x >= MARGIN && x <= MARGIN + 120 && y >= 276 && y <= 312) {
    currentMode = MORE_VIEW;
    screenDirty = true;
    return true;
  }
  if (managedYeastCount <= 0) return false;
  if (x >= MARGIN && x <= MARGIN + 72 && y >= 214 && y <= 250) {
    manageYeastIndex = manageYeastIndex <= 0 ? managedYeastCount - 1 : manageYeastIndex - 1;
    screenDirty = true;
    return true;
  }
  if (x >= UI_W - MARGIN - 72 && x <= UI_W - MARGIN && y >= 214 && y <= 250) {
    manageYeastIndex = (manageYeastIndex + 1) % managedYeastCount;
    screenDirty = true;
    return true;
  }
  if (x >= MARGIN + 84 && x <= MARGIN + 194 && y >= 214 && y <= 250) {
    beginNewYeastWizard(managedYeastIds[manageYeastIndex]);
    return true;
  }
  if (x >= MARGIN + 206 && x <= MARGIN + 316 && y >= 214 && y <= 250) {
    if (mountSDTemporarily()) {
      YeastPresetRepository::deleteCustom(managedYeastIds[manageYeastIndex]);
      dismountSD();
    }
    loadManagedYeasts();
    screenDirty = true;
    return true;
  }
  return false;
}

int batchNumberFromId(const char* id) {
  int n = 0;
  if (sscanf(id, "batch_%d", &n) == 1) return n;
  return 0;
}

void loadManagedBatches() {
  managedBatchCount = 0;
  if (!mountSDTemporarily()) return;
  if (!SD.exists("/data/batches")) {
    dismountSD();
    return;
  }
  File dir = SD.open("/data/batches");
  if (!dir) {
    dismountSD();
    return;
  }
  File entry = dir.openNextFile();
  while (entry && managedBatchCount < 16) {
    if (entry.isDirectory()) {
      const char* name = entry.name();
      const char* slash = strrchr(name, '/');
      const char* id = slash ? slash + 1 : name;
      static BrewProfile p;
      if (BrewProfileStore::load(id, &p)) {
        strncpy(managedBatchIds[managedBatchCount], id, 23);
        managedBatchIds[managedBatchCount][23] = '\0';
        strncpy(managedBatchNames[managedBatchCount], p.batchName, 39);
        managedBatchNames[managedBatchCount][39] = '\0';
        managedBatchCount++;
      }
    }
    entry.close();
    entry = dir.openNextFile();
  }
  dir.close();
  dismountSD();
  if (manageBatchIndex >= managedBatchCount) manageBatchIndex = max(0, managedBatchCount - 1);
}

int nextBatchNumberOnSD() {
  int highest = 0;
  if (!SD.exists("/data/batches")) return 1;
  File dir = SD.open("/data/batches");
  if (!dir) return 1;
  File entry = dir.openNextFile();
  while (entry) {
    if (entry.isDirectory()) {
      const char* name = entry.name();
      const char* slash = strrchr(name, '/');
      const char* id = slash ? slash + 1 : name;
      int n = batchNumberFromId(id);
      if (n > highest) highest = n;
    }
    entry.close();
    entry = dir.openNextFile();
  }
  dir.close();
  return highest + 1;
}

void continueManagedBatch(const char* batchId) {
  if (!mountSDTemporarily()) return;
  if (BrewProfileStore::load(batchId, &activeBrewProfile)) {
    if (activeBrewProfile.completed) {
      LOG_INFO("Batch %s is completed; not continuing as active\n", batchId);
      dismountSD();
      currentMode = MANAGE_BREW_VIEW;
      screenDirty = true;
      return;
    }
    bool logReady = ensureFermentationLogFile(activeBrewProfile.batchId);
    BrewProfileStore::logPath(activeBrewProfile.batchId, currentFermentationFile, sizeof(currentFermentationFile));
    fermentationFileOpen = logReady;
    brewProfileLoaded = true;
    BrewProfileStore::saveActiveBatchId(activeBrewProfile.batchId);
    targetCurveAvailable = SD.exists("/data") && TargetCurveGenerator::generateAndSave(activeBrewProfile);
    if (logReady) loadHistoricalDataFromCSV(currentFermentationFile, currentLoadMode, MAX_DATA_POINTS, 1);
    refreshFermentationAssistantFromProfile();
  }
  dismountSD();
  currentMode = DASHBOARD_VIEW;
  screenDirty = true;
}

void copyManagedBatch(const char* batchId) {
  if (!mountSDTemporarily()) return;
  static BrewProfile p;
  if (BrewProfileStore::load(batchId, &p)) {
    BrewProfileStore::buildBatchId(nextBatchNumberOnSD(), p.batchId, sizeof(p.batchId));
    char copiedName[40];
    snprintf(copiedName, sizeof(copiedName), "%s Copy", p.batchName);
    strncpy(p.batchName, copiedName, sizeof(p.batchName) - 1);
    p.batchName[sizeof(p.batchName) - 1] = '\0';
    p.createdAt = getCurrentEpoch();
    p.fermentationStartAt = 0;
    p.completed = false;
    p.completedAt = 0;
    p.dryHopDone = false;
    p.dryHopSkipped = false;
    p.dryHopStartTime = 0;
    p.dryHopRemoved = false;
    p.dryHopRemoveSkipped = false;
    p.dryHopRemovedAt = 0;
    p.dRestDone = false;
    p.dRestSkipped = false;
    p.dRestStartedAt = 0;
    p.coldCrashDone = false;
    p.coldCrashSkipped = false;
    p.coldCrashStartedAt = 0;
    p.packageStarted = false;
    p.packageStartedAt = 0;
    p.packageDone = false;
    p.packageSkipped = false;
    p.packagedAt = 0;
    p.measuredOG = 0.0f;
    p.ogDifference = 0.0f;
    p.ogVerified = false;
    p.ogNeedsChoice = false;
    p.floatInBrewConfirmed = false;
    p.floatInBrewAt = 0;
    BrewProfileStore::save(p);
    TargetCurveGenerator::generateAndSave(p);
    activeBrewProfile = p;
    bool logReady = ensureFermentationLogFile(activeBrewProfile.batchId);
    BrewProfileStore::logPath(activeBrewProfile.batchId, currentFermentationFile, sizeof(currentFermentationFile));
    fermentationFileOpen = logReady;
    brewProfileLoaded = true;
    BrewProfileStore::saveActiveBatchId(activeBrewProfile.batchId);
    clearHistoricalDisplayData();
    refreshFermentationAssistantFromProfile();
  }
  dismountSD();
  loadManagedBatches();
  currentMode = DASHBOARD_VIEW;
  screenDirty = true;
}

void buildManagedBatchChildPath(const char* parentPath, const char* entryName, char* path, size_t pathSize) {
  if (!entryName || entryName[0] == '\0') {
    snprintf(path, pathSize, "%s", parentPath);
    return;
  }
  if (strchr(entryName, '/')) {
    snprintf(path, pathSize, "%s", entryName);
    return;
  }
  snprintf(path, pathSize, "%s/%s", parentPath, entryName);
}

bool deleteManagedBatchPath(const char* path) {
  File entry = SD.open(path);
  if (!entry) return !SD.exists(path);

  if (!entry.isDirectory()) {
    entry.close();
    return SD.remove(path);
  }

  File child = entry.openNextFile();
  bool ok = true;
  while (child) {
    char childPath[96];
    buildManagedBatchChildPath(path, child.name(), childPath, sizeof(childPath));
    child.close();
    ok = deleteManagedBatchPath(childPath) && ok;
    child = entry.openNextFile();
  }
  entry.close();
  return SD.rmdir(path) && ok;
}

void deleteManagedBatch(const char* batchId) {
  if (!mountSDTemporarily()) return;
  char activeBatchId[24];
  bool deletingActive =
    strcmp(activeBrewProfile.batchId, batchId) == 0 ||
    (BrewProfileStore::loadActiveBatchId(activeBatchId, sizeof(activeBatchId)) &&
     strcmp(activeBatchId, batchId) == 0);

  char path[64];
  snprintf(path, sizeof(path), "/data/batches/%s", batchId);
  bool deleted = deleteManagedBatchPath(path);
  if (!deleted) {
    LOG_ERROR("Failed to delete batch directory: %s\n", path);
  }

  if (deletingActive) {
    brewProfileLoaded = false;
    fermentationFileOpen = false;
    currentFermentationFile[0] = '\0';
    BrewProfileStore::clearActiveBatchId();
    clearHistoricalDisplayData();
  }
  dismountSD();
  loadManagedBatches();
  screenDirty = true;
}
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
